nicholasnloehrke/87s_research/boards/controller/pcb/symbols/PJSD03TS-AU_R1_000A1/PJSD03TS-AU_R1_000A1.step

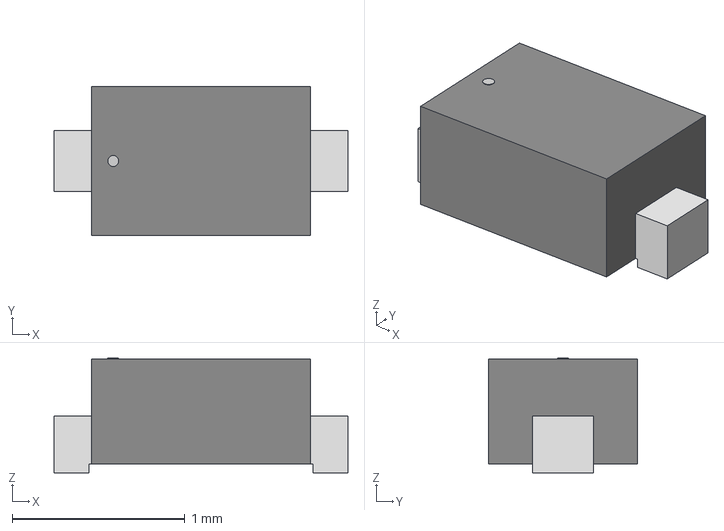
[picture p28: CAD file, 2025-05-06]
boards/controller/pcb/symbols/PJSD03TS-AU_R1_000A1/PJSD03TS-AU_R1_000A1.step
1.70 x 0.864 x 0.663 mm
