nicholasnloehrke/87s_research/boards/controller/pcb/symbols/RH100-16.000-18-2030-EXT-TR/RH100-16.000-18-2030-EXT-TR.step

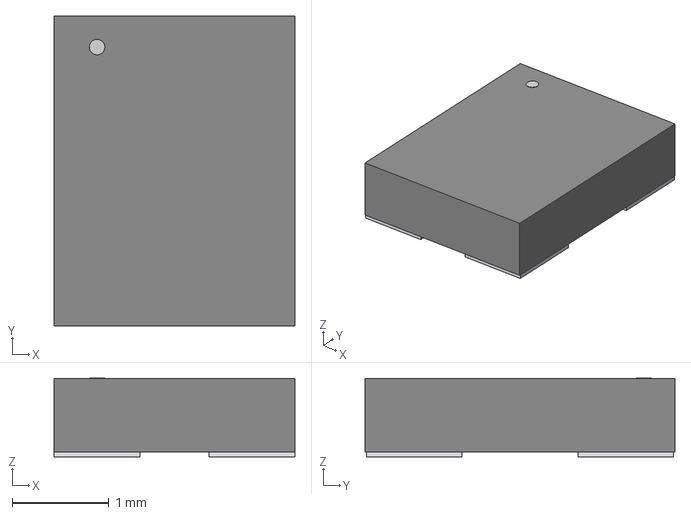
[picture p29: CAD file, 2025-05-06]
boards/controller/pcb/symbols/RH100-16.000-18-2030-EXT-TR/RH100-16.000-18-2030-EXT-TR.step
2.49 x 3.20 x 0.815 mm
