nicholasnloehrke/87s_research/boards/controller/pcb/symbols/SISA35DN-T1-GE3/SISA35DN-T1-GE3.STEP

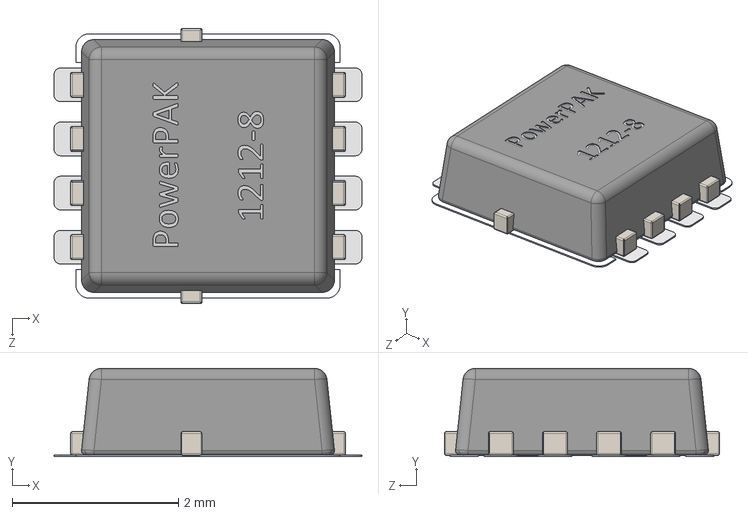
[picture p30: CAD file, 2024-11-11]
boards/controller/pcb/symbols/SISA35DN-T1-GE3/SISA35DN-T1-GE3.STEP
3.70 x 1.06 x 3.30 mm
