nicholasnloehrke/87s_research/boards/controller/pcb/symbols/SSM3J372R_LF/SSM3J372R_LF.step

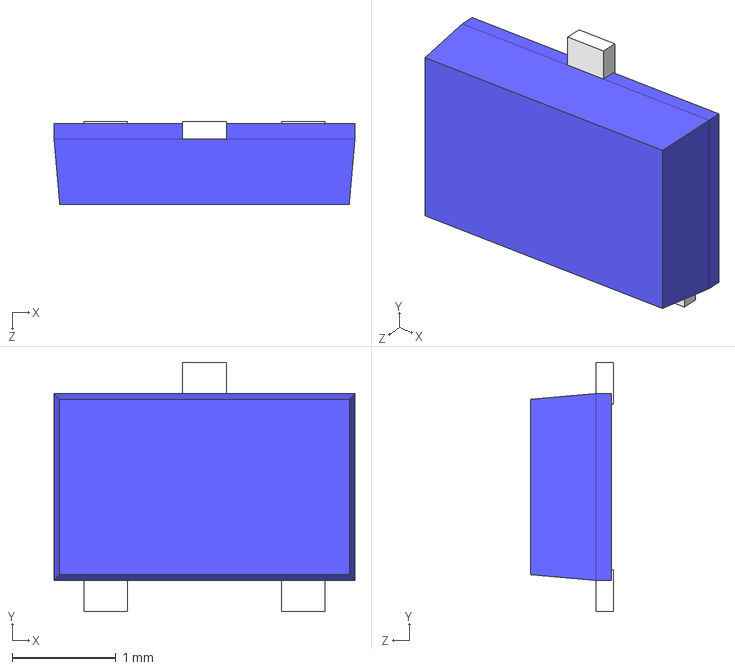
[picture p31: CAD file, 2025-05-06]
boards/controller/pcb/symbols/SSM3J372R_LF/SSM3J372R_LF.step
2.90 x 2.40 x 0.8 mm
