nicholasnloehrke/87s_research/boards/controller/pcb/symbols/XT30/XT30.stp

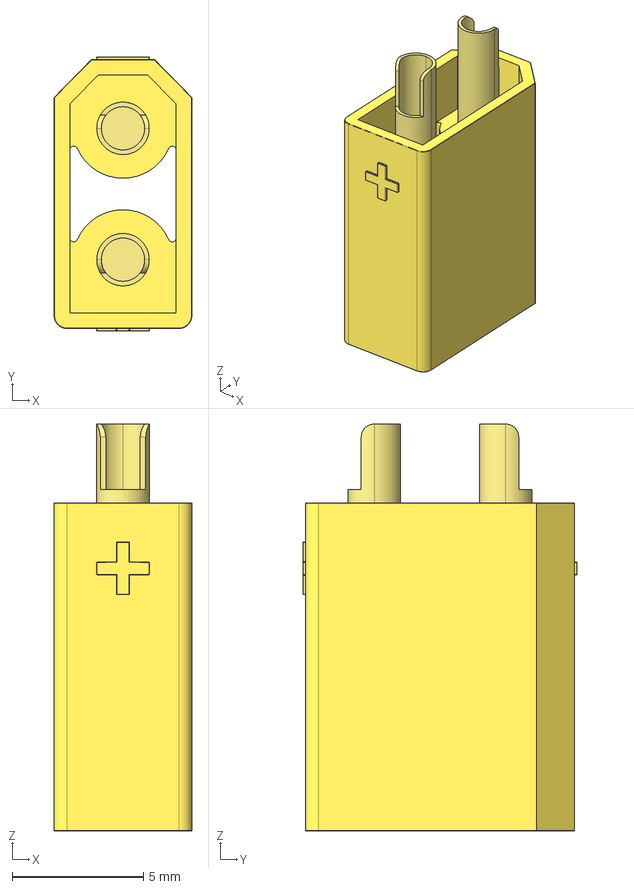
[picture p32: CAD file, 2024-11-11]
boards/controller/pcb/symbols/XT30/XT30.stp
5.25 x 10.4 x 15.5 mm
