nicholasnloehrke/87s_research/boards/controller_mockup/mockup_for_reference_only/mockup/300SPxJ1xxxM2xE.stp

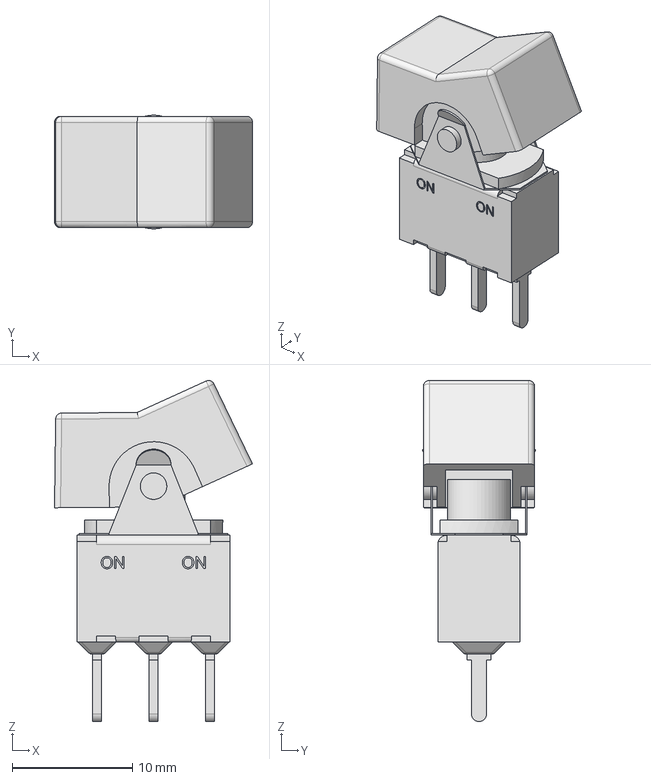
[picture p33: CAD file, 2025-03-07]
boards/controller_mockup/mockup_for_reference_only/mockup/300SPxJ1xxxM2xE.stp
16.5 x 9.45 x 28.4 mm
