nicholasnloehrke/87s_research/boards/controller_mockup/mockup_for_reference_only/mockup/USB4120_03_C/USB4120-03-C.step

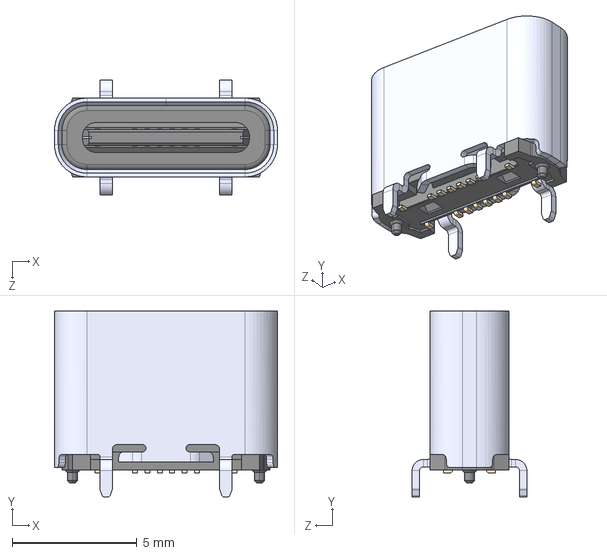
[picture p34: CAD file, 2025-03-07]
boards/controller_mockup/mockup_for_reference_only/mockup/USB4120_03_C/USB4120-03-C.step
8.94 x 7.45 x 4.60 mm
