nicholasnloehrke/87s_research/boards/power_supply/pcb/symbols/1N4148W-13-F/1N4148W-13-F.STEP

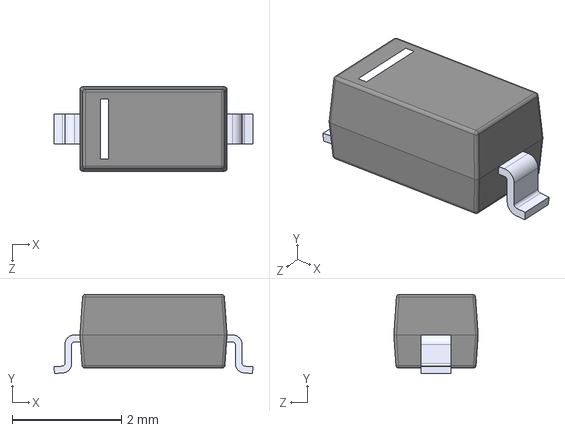
[picture p35: CAD file, 2024-11-08]
boards/power_supply/pcb/symbols/1N4148W-13-F/1N4148W-13-F.STEP
3.65 x 1.45 x 1.55 mm
