nicholasnloehrke/87s_research/boards/power_supply/pcb/symbols/LM5181NGUR/LM5181NGUR.stp

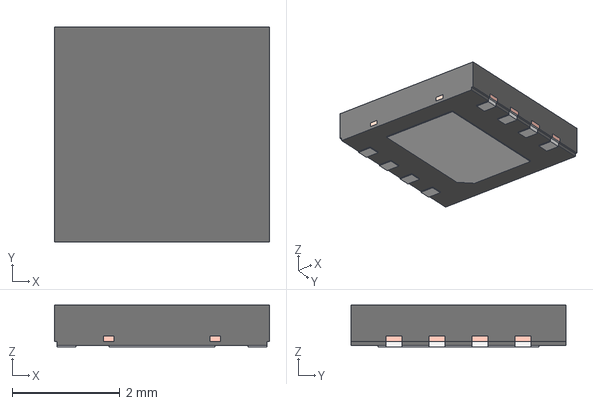
[picture p36: CAD file, 2024-09-19]
boards/power_supply/pcb/symbols/LM5181NGUR/LM5181NGUR.stp
4.00 x 4.00 x 0.775 mm
BODY-SON_AF0
FRAME-NGU0008C_AF0
