nicholasnloehrke/87s_research/boards/power_supply/pcb/symbols/MP2759GQ-0000-Z/MP2759GQ-0000-Z.iges

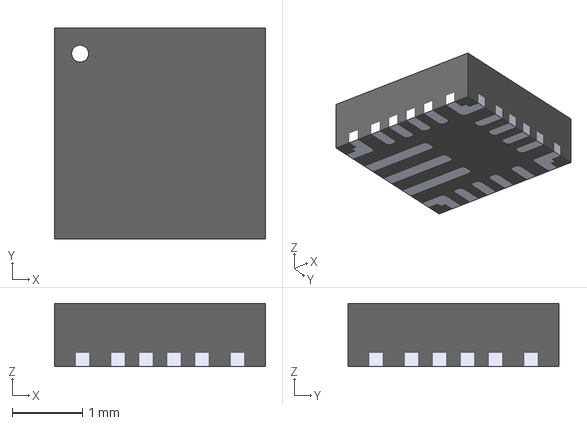
[picture p37: CAD file, 2024-11-11]
boards/power_supply/pcb/symbols/MP2759GQ-0000-Z/MP2759GQ-0000-Z.iges
3.00 x 3.00 x 0.9 mm
