nicholasnloehrke/87s_research/boards/power_supply/pcb/symbols/PTS526_SK15_SMTR2_LFS/PTS526_SK15_SMTR2_LFS.STEP

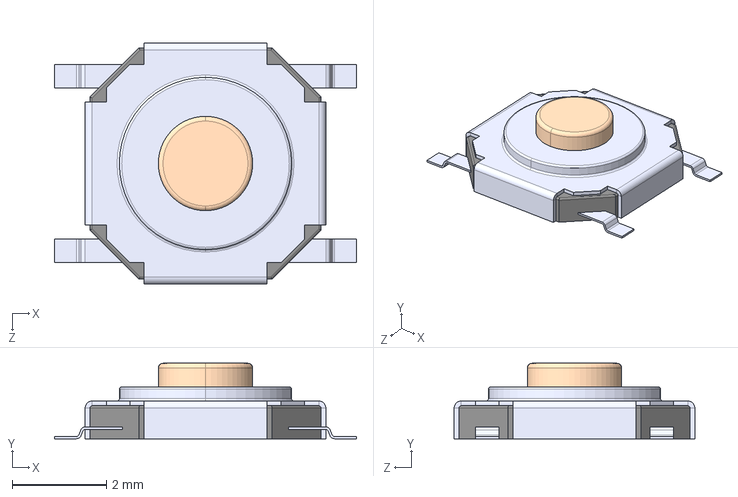
[picture p38: CAD file, 2024-10-13]
boards/power_supply/pcb/symbols/PTS526_SK15_SMTR2_LFS/PTS526_SK15_SMTR2_LFS.STEP
6.40 x 1.60 x 5.10 mm
