nicholasnloehrke/87s_research/boards/power_supply/pcb/symbols/SK34SMA-3G/SK34SMA-3G.step

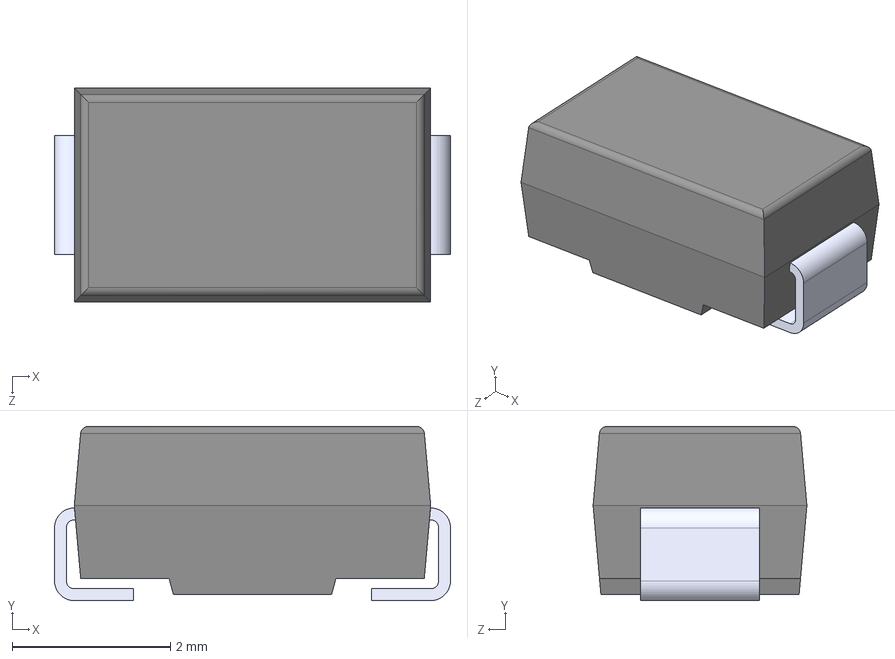
[picture p39: CAD file, 2024-11-08]
boards/power_supply/pcb/symbols/SK34SMA-3G/SK34SMA-3G.step
5.00 x 2.20 x 2.70 mm
