nicholasnloehrke/87s_research/boards/power_supply/pcb/symbols/SMAZ22-13-F/SMAZ22-13-F.step

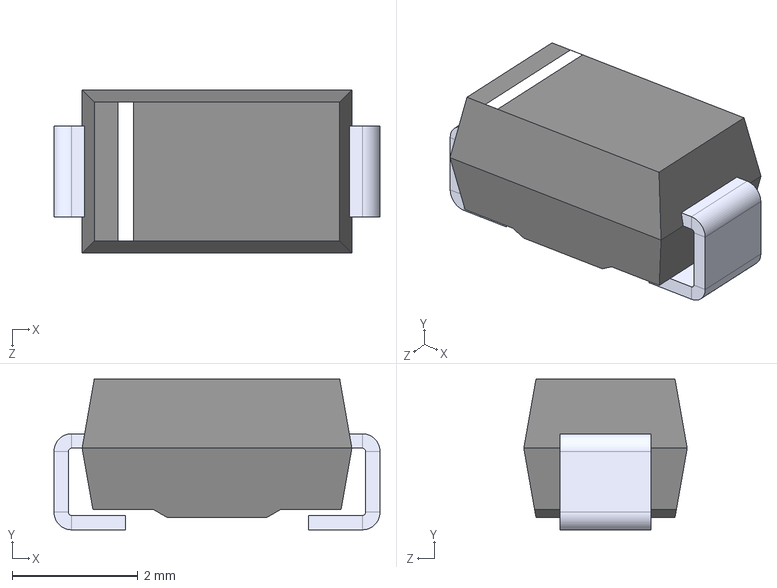
[picture p40: CAD file, 2024-11-11]
boards/power_supply/pcb/symbols/SMAZ22-13-F/SMAZ22-13-F.step
5.20 x 2.40 x 2.60 mm
