nicholasnloehrke/87s_research/boards/power_supply/pcb/symbols/USB4105-GF-A/USB4105-GF-A.step

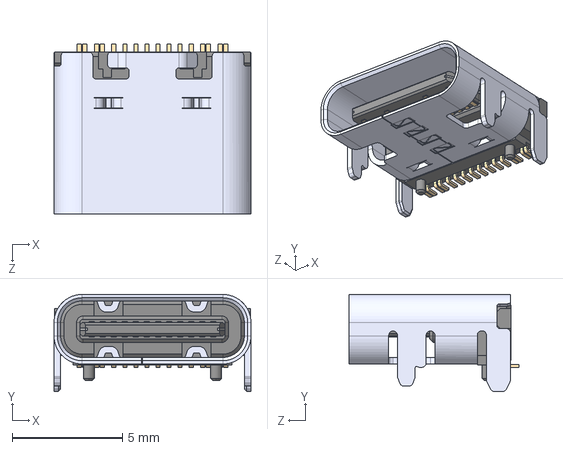
[picture p41: CAD file, 2024-11-11]
boards/power_supply/pcb/symbols/USB4105-GF-A/USB4105-GF-A.step
8.94 x 4.41 x 7.71 mm
