nicholasnloehrke/87s_research/boards/power_supply/pcb/symbols/USBLC6-2SC6/USBLC6-2SC6.step

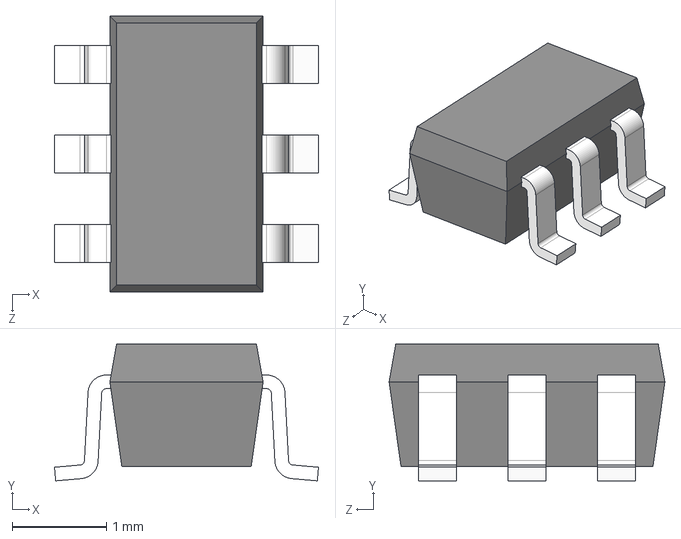
[picture p42: CAD file, 2024-11-08]
boards/power_supply/pcb/symbols/USBLC6-2SC6/USBLC6-2SC6.step
2.80 x 1.45 x 2.92 mm
