nicholasnloehrke/87s_research/kicad/power_supply/symbols/750313445/SOIC_13445_WRE.step

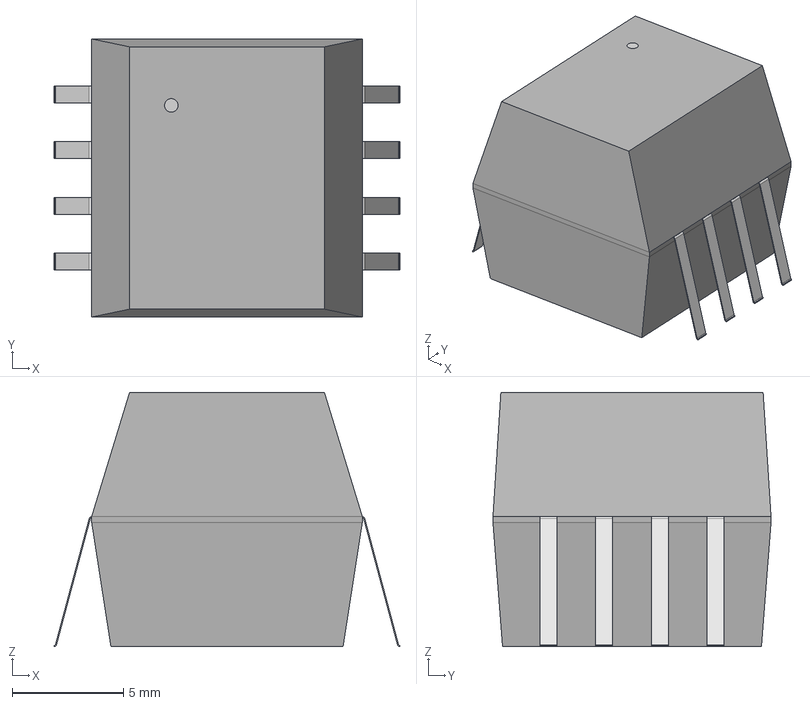
[picture p43: CAD file, 2024-09-19]
kicad/power_supply/symbols/750313445/SOIC_13445_WRE.step
15.5 x 12.5 x 11.4 mm
