nicholasnloehrke/87s_research/kicad/power_supply/symbols/DMN65D8L_7/SOT-23_2P9X1P3_DIO.step

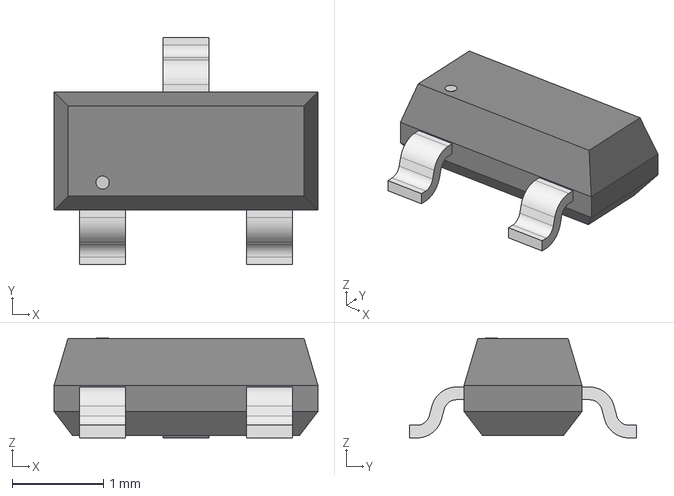
[picture p44: CAD file, 2024-09-16]
kicad/power_supply/symbols/DMN65D8L_7/SOT-23_2P9X1P3_DIO.step
2.90 x 2.49 x 1.09 mm
