nicholasnloehrke/87s_research/kicad/power_supply/symbols/PDZVTR9_1B/DIO_PDZVTFT_ROM.step

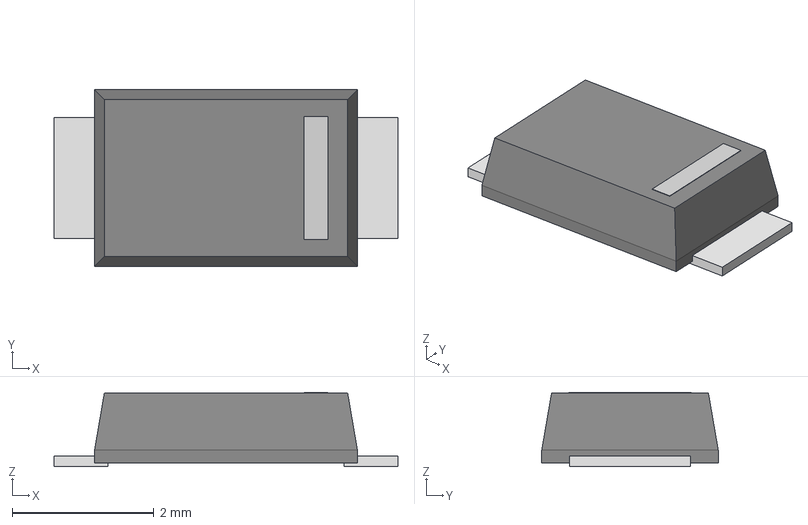
[picture p45: CAD file, 2024-09-19]
kicad/power_supply/symbols/PDZVTR9_1B/DIO_PDZVTFT_ROM.step
4.85 x 2.49 x 1.05 mm
