nicholasnloehrke/87s_research/kicad/power_supply/symbols/RTBS60M/RTBS60M.step

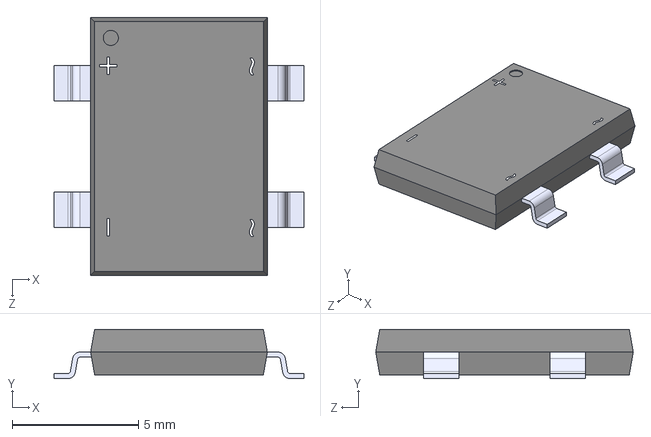
[picture p46: CAD file, 2024-09-16]
kicad/power_supply/symbols/RTBS60M/RTBS60M.step
9.90 x 1.95 x 10.2 mm
