nicholasnloehrke/87s_research/kicad/power_supply/symbols/SISS94DN_T1_GE3/model/SISS94DN-T1-GE3.FCStd

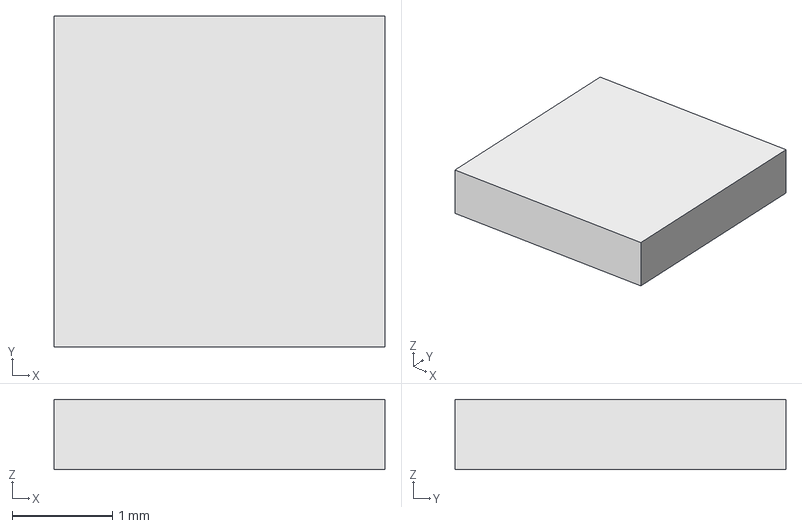
[picture p47: CAD file, 2024-09-24]
kicad/power_supply/symbols/SISS94DN_T1_GE3/model/SISS94DN-T1-GE3.FCStd
3.30 x 3.30 x 0.7 mm
