nicholasnloehrke/87s_research/kicad/power_supply/symbols/TPS562243DRLR/DRL0006A.stp

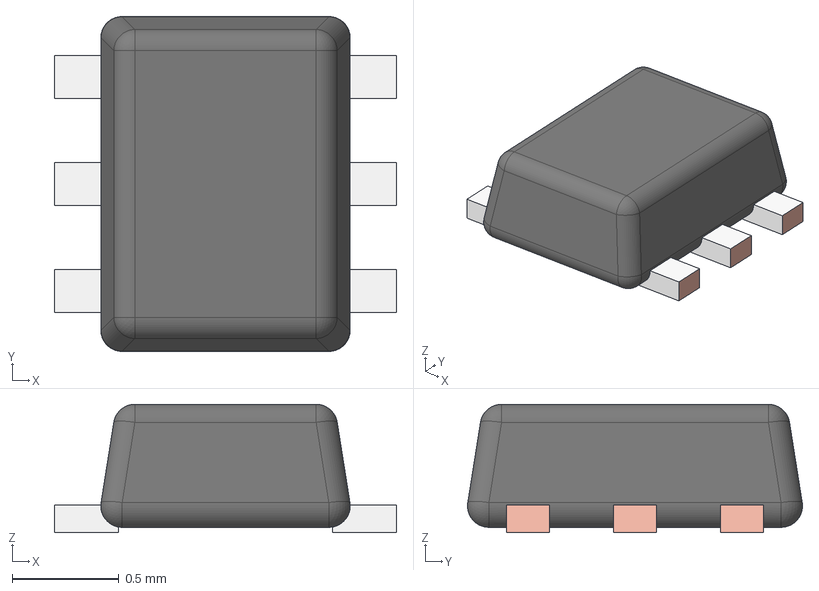
[picture p48: CAD file, 2024-10-03]
kicad/power_supply/symbols/TPS562243DRLR/DRL0006A.stp
1.60 x 1.57 x 0.6 mm
FRAME-DRL0006A
BODY-SOT
PIN1-ID
