nicholasnloehrke/87s_research/mechanical/encoder_pec12r-4x20f-sxxxx.stp

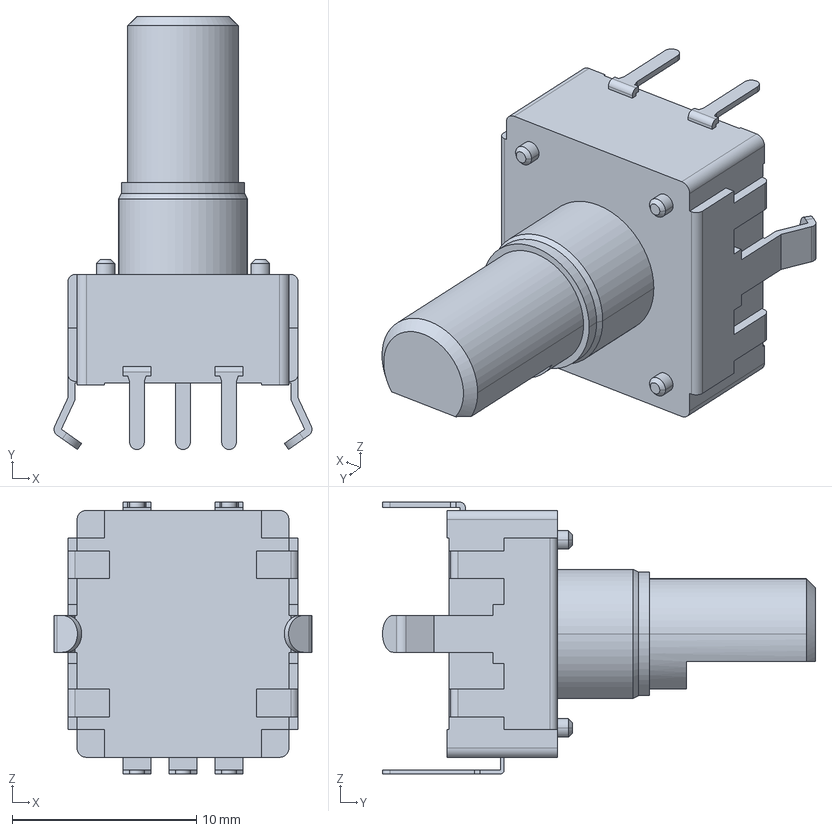
[picture p49: CAD file, 2025-02-06]
mechanical/encoder_pec12r-4x20f-sxxxx.stp
14.0 x 23.5 x 14.7 mm
