nicholasnloehrke/87s_research/boards/controller_mockup/mockup_for_reference_only/mockup/Unnamed2-P__E-Switch Secure_3D_MODELS_STP_FORMAT_300SPxJ1xxxM2xE.stp.step

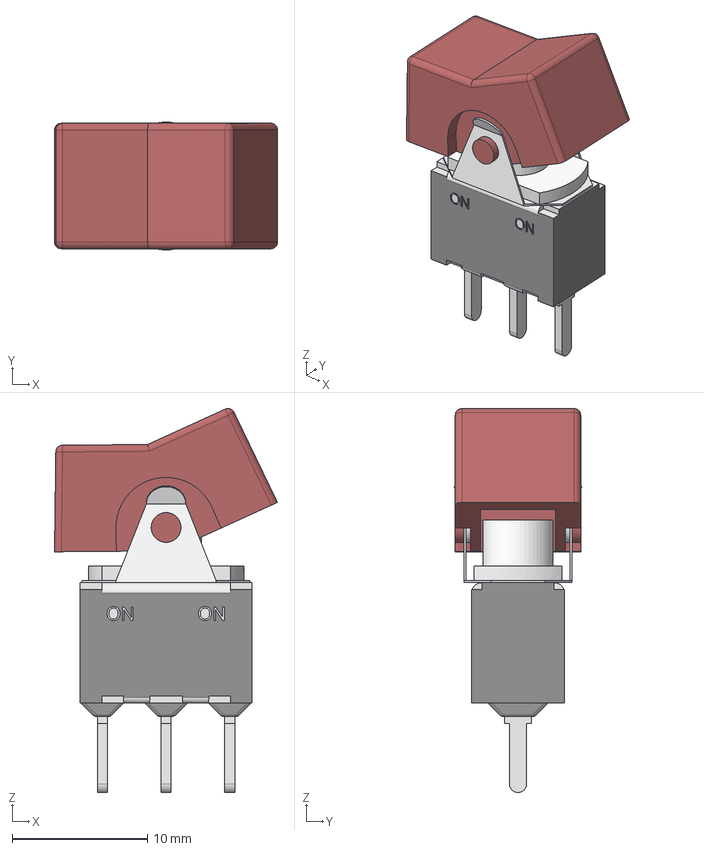
[picture p50: CAD file, 2025-03-07]
boards/controller_mockup/mockup_for_reference_only/mockup/Unnamed2-P__E-Switch Secure_3D_MODELS_STP_FORMAT_300SPxJ1xxxM2xE.stp.step
16.5 x 9.45 x 28.4 mm
