nicholasnloehrke/87s_research/boards/controller_mockup/mockup_for_reference_only/mockup/encoder-with-color.step

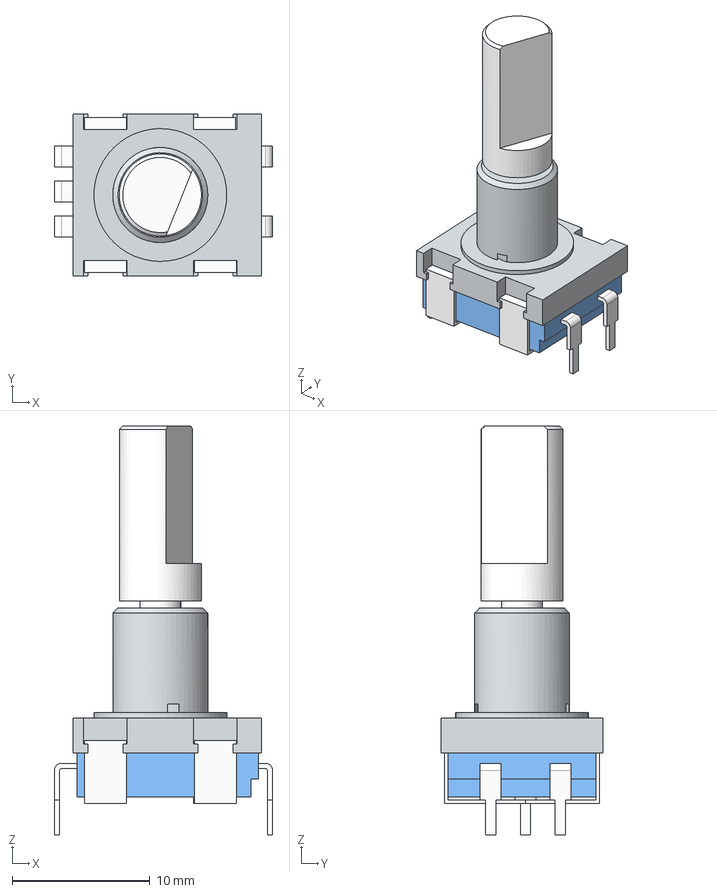
[picture p51: CAD file, 2025-03-07]
boards/controller_mockup/mockup_for_reference_only/mockup/encoder-with-color.step
15.8 x 11.8 x 29.7 mm
mtg flange
pins_encoder body_2 x 5
shaft_encoder
body_encoder
