nicholasnloehrke/87s_research/boards/controller-old/pcb/controller.kicad_pcb

## KiCad design boards/controller-old/pcb/controller.kicad_pcb (2024-11-23, an earlier design)

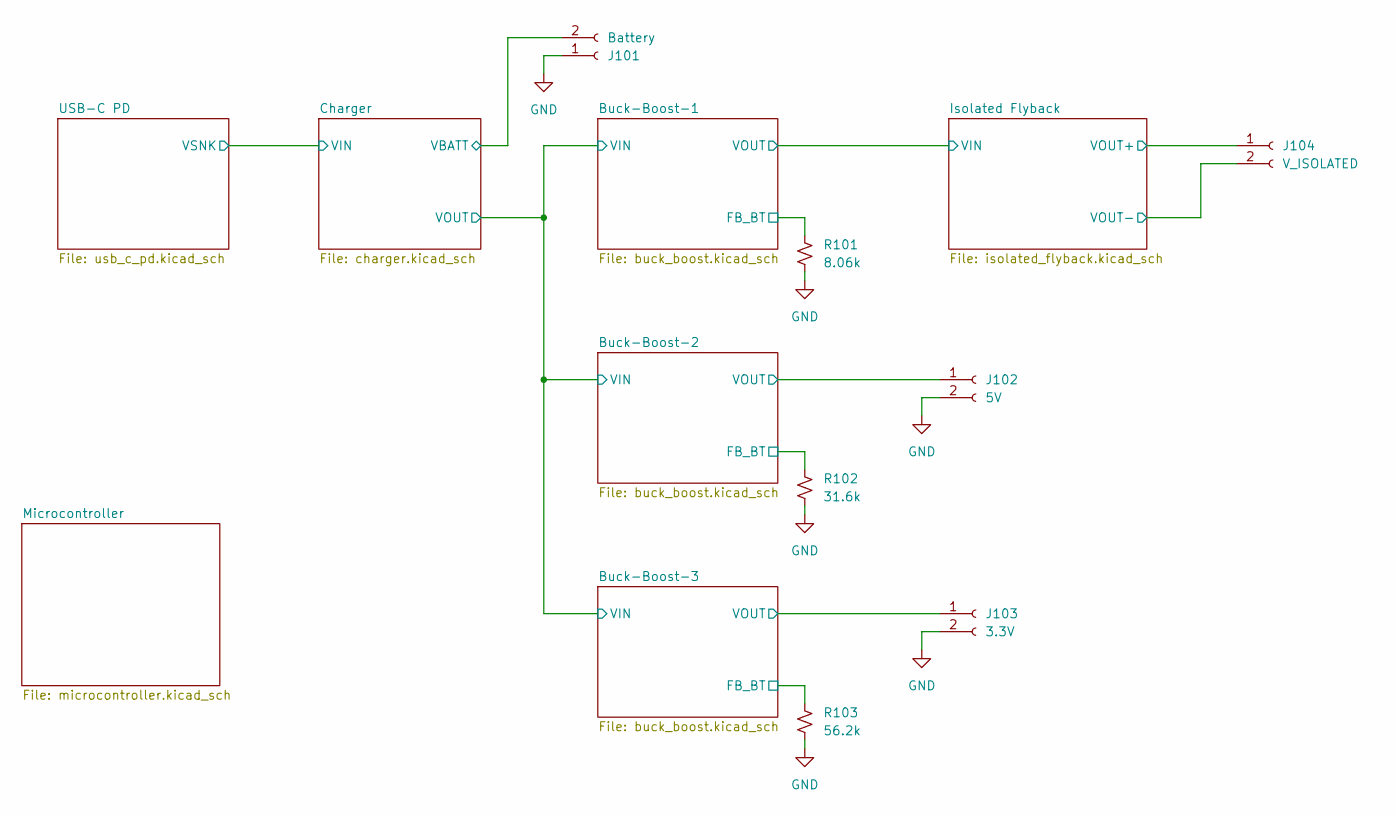
[picture p77: schematic controller.kicad_sch, Power Supply]

Parts:
J101: Battery; AMASS_XT30U-F_1x02_P5.0mm_Vertical
J102: 5V; JST_XH_B2B-XH-A_1x02_P2.50mm_Vertical
J103: 3.3V; JST_XH_B2B-XH-A_1x02_P2.50mm_Vertical
J104: V_ISOLATED; JST_XH_B2B-XH-A_1x02_P2.50mm_Vertical
R101: 8.06k; R_0603_1608Metric
R102: 31.6k; R_0603_1608Metric
R103: 56.2k; R_0603_1608Metric

Connections:
/Buck-Boost-1/FB_BT: R101.2; also elsewhere on the board
/Buck-Boost-2/FB_BT: R102.2; also elsewhere on the board
/Buck-Boost-2/VOUT: J102.1; also elsewhere on the board
/Buck-Boost-3/FB_BT: R103.2; also elsewhere on the board
/Buck-Boost-3/VOUT: J103.1; also elsewhere on the board
/Charger/VBATT: J101.2; also elsewhere on the board
/Isolated Flyback/VOUT+: J104.1; also elsewhere on the board
/Isolated Flyback/VOUT-: J104.2; also elsewhere on the board
GND: J101.1, J102.2, J103.2, R101.1, R102.1, R103.1; also elsewhere on the board

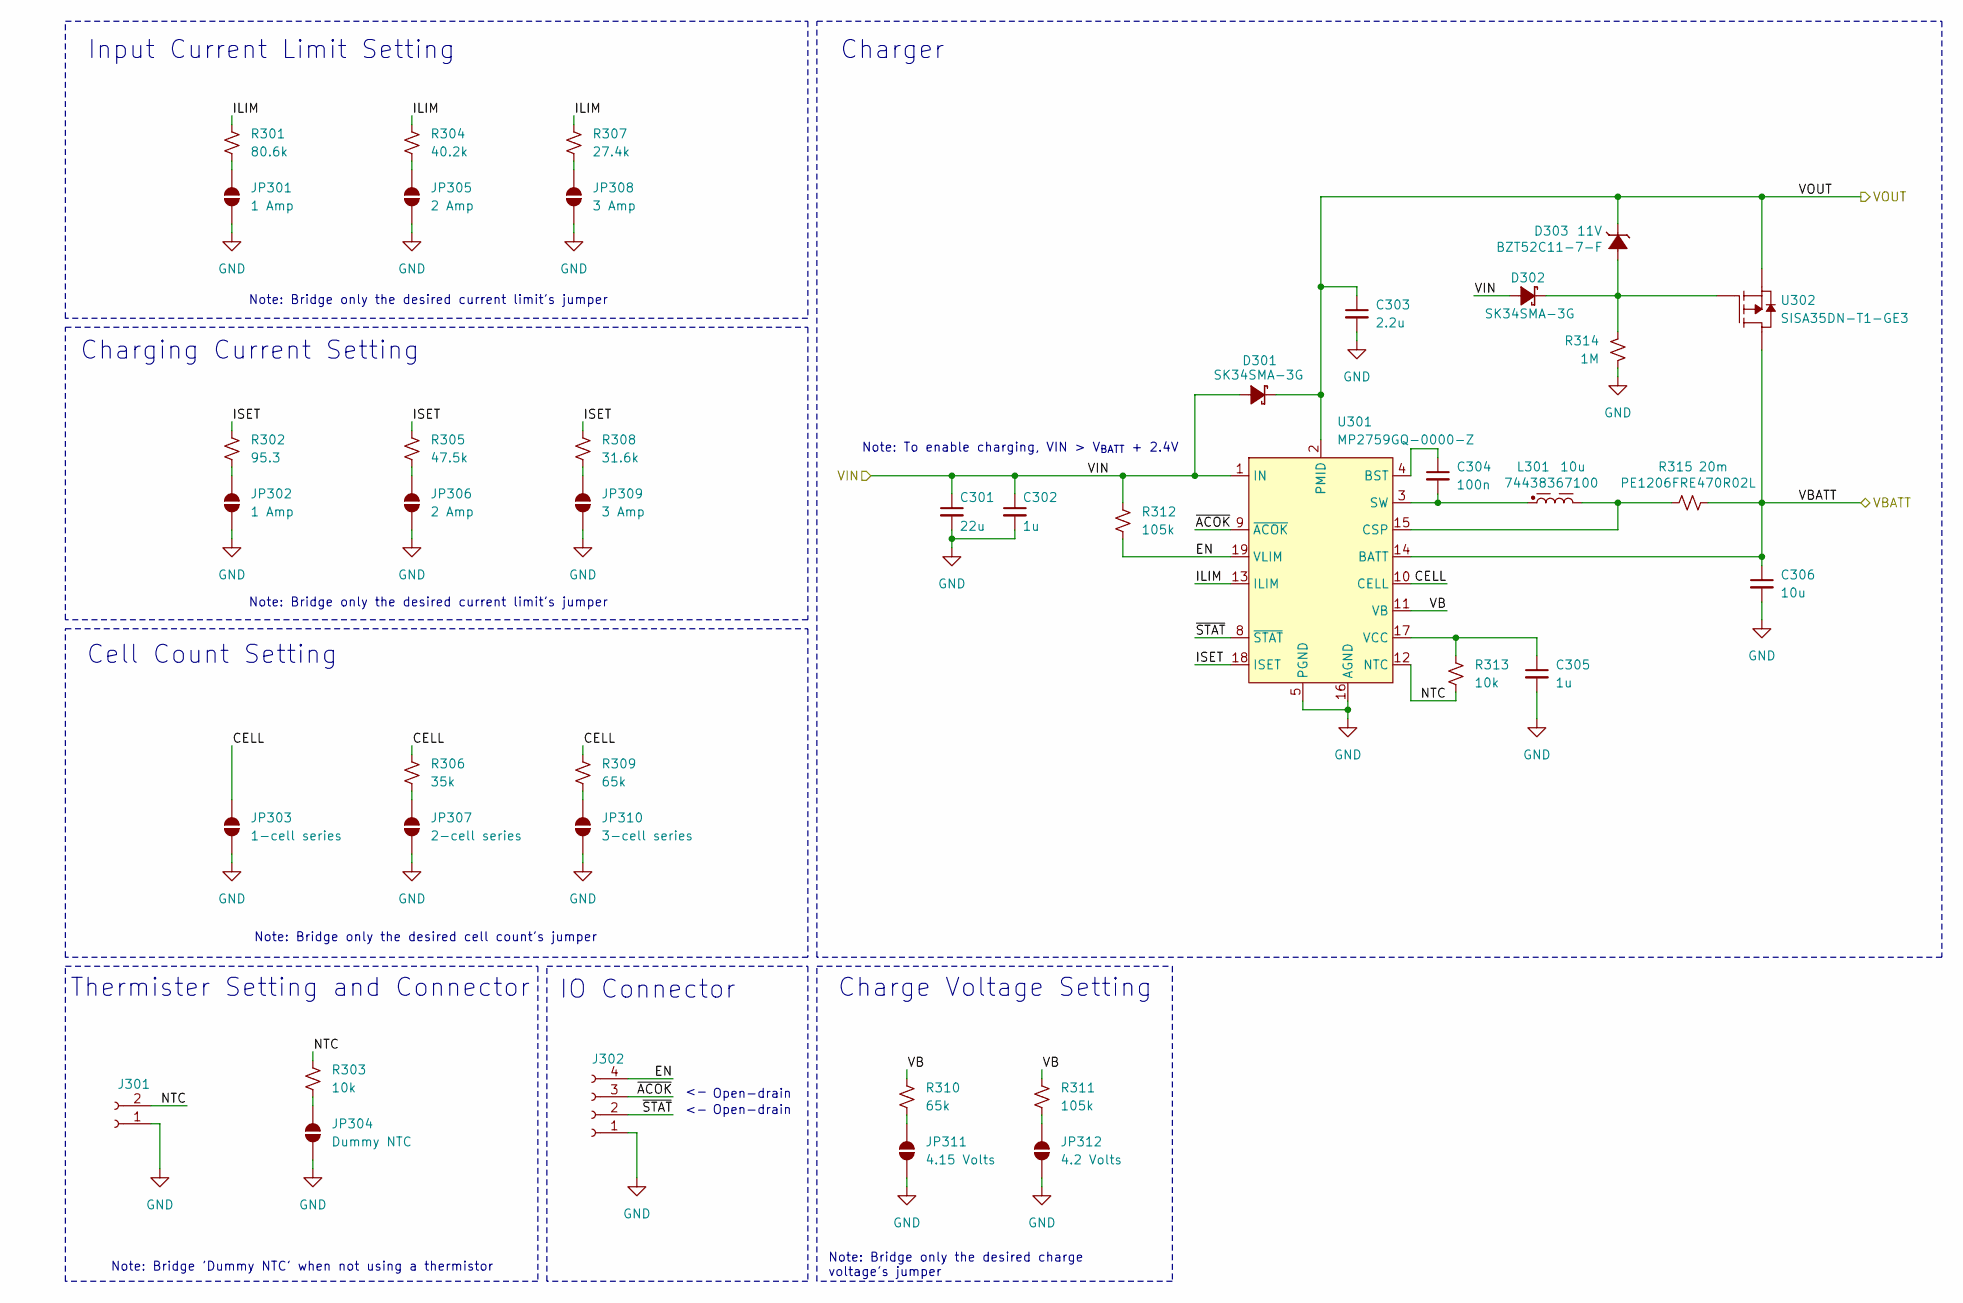
[picture p78: schematic charger.kicad_sch]

Parts:
C301: 22u; C_1206_3216Metric
C302, C305: 1u; C_0603_1608Metric
C303: 2.2u; C_1206_3216Metric
C304: 100n; C_0603_1608Metric
C306: 10u; C_0805_2012Metric
D301, D302: SK34SMA-3G; MPN SK34SMA-3G
D303: 11V; BZT52C11-7-F; MPN BZT52C11-7-F
J301: Conn_01x02_Socket; JST_XH_B2B-XH-A_1x02_P2.50mm_Vertical
J302: Conn_01x04_Socket; JST_XH_B4B-XH-A_1x04_P2.50mm_Vertical
JP301, JP302: 1 Amp; SolderJumper-2_P1.3mm_Open_RoundedPad1.0x1.5mm
JP303: 1-cell series; SolderJumper-2_P1.3mm_Open_RoundedPad1.0x1.5mm
JP304: Dummy NTC; SolderJumper-2_P1.3mm_Open_RoundedPad1.0x1.5mm
JP305, JP306: 2 Amp; SolderJumper-2_P1.3mm_Open_RoundedPad1.0x1.5mm
JP307: 2-cell series; SolderJumper-2_P1.3mm_Open_RoundedPad1.0x1.5mm
JP308, JP309: 3 Amp; SolderJumper-2_P1.3mm_Open_RoundedPad1.0x1.5mm
JP310: 3-cell series; SolderJumper-2_P1.3mm_Open_RoundedPad1.0x1.5mm
JP311: 4.15 Volts; SolderJumper-2_P1.3mm_Open_RoundedPad1.0x1.5mm
JP312: 4.2 Volts; SolderJumper-2_P1.3mm_Open_RoundedPad1.0x1.5mm
L301: 10u; 74438367100; MPN 74438367100
R301: 80.6k; R_0603_1608Metric
R302: 95.3; R_0603_1608Metric
R303, R313: 10k; R_0603_1608Metric
R304: 40.2k; R_0603_1608Metric
R305: 47.5k; R_0603_1608Metric
R306: 35k; R_0603_1608Metric
R307: 27.4k; R_0603_1608Metric
R308: 31.6k; R_0603_1608Metric
R309, R310: 65k; R_0603_1608Metric
R311, R312: 105k; R_0603_1608Metric
R314: 1M; R_0603_1608Metric
R315: 20m; PE1206FRE470R02L; MPN PE1206FRE470R02L
U301: MP2759GQ-0000-Z; MPN MP2759GQ-0000-Z
U302: SISA35DN-T1-GE3; MPN SISA35DN-T1-GE3

Connections:
/Buck-Boost-1/VIN: C303.1, D301.1, D303.1, U301.2 (PMID), U302.1; also elsewhere on the board
/Charger/CELL: JP303.2 (B), R306.1, R309.1, U301.10 (CELL)
/Charger/EN: J302.4, R312.2, U301.19 (VLIM)
/Charger/ILIM: R301.1, R304.1, R307.1, U301.13 (ILIM)
/Charger/ISET: R302.1, R305.1, R308.1, U301.18 (ISET)
/Charger/NTC: J301.2, R303.1, R313.2, U301.12 (NTC)
/Charger/VB: R310.1, R311.1, U301.11 (VB)
/Charger/VBATT: C306.1, R315.2, U301.14 (BATT), U302.5; also elsewhere on the board
/Charger/VIN: C301.1, C302.1, D301.2, D302.2, R312.1, U301.1 (IN); also elsewhere on the board
/Charger/~ACOK: J302.3, U301.9 (~ACOK)
/Charger/~STAT: J302.2, U301.8 (~STAT)
GND: C301.2, C302.2, C303.2, C305.2, C306.2, J301.1, J302.1, JP301.1 (A), JP302.1 (A), JP303.1 (A), JP304.1 (A), JP305.1 (A), JP306.1 (A), JP307.1 (A), JP308.1 (A), JP309.1 (A), JP310.1 (A), JP311.1 (A), JP312.1 (A), R314.2, U301.5 (PGND), U301.6 (PGND), U301.7 (PGND), U301.16 (AGND); also elsewhere on the board
unnamed: D302.1, D303.2, R314.1, U302.4
unnamed: JP301.2 (B), R301.2
unnamed: JP302.2 (B), R302.2
unnamed: JP304.2 (B), R303.2
unnamed: JP305.2 (B), R304.2
unnamed: JP306.2 (B), R305.2
unnamed: JP307.2 (B), R306.2
unnamed: JP308.2 (B), R307.2
unnamed: JP309.2 (B), R308.2
unnamed: JP310.2 (B), R309.2
unnamed: JP311.2 (B), R310.2
unnamed: JP312.2 (B), R311.2
unnamed: C304.1, U301.4 (BST)
unnamed: L301.2, R315.1, U301.15 (CSP)
unnamed: C304.2, L301.1, U301.3 (SW)
unnamed: C305.1, R313.1, U301.17 (VCC)

Notes on the sheet:
Note: Bridge only the desired cell count's jumper
Charging Current Setting
Note: Bridge 'Dummy NTC' when not using a thermistor
Thermister Setting and Connector
Cell Count Setting
Charger
Note: Bridge only the desired charge voltage's jumper
IO Connector
Input Current Limit Setting
Note: Bridge only the desired current limit's jumper
Open-drain
Note: To enable charging, VIN > V_{BATT} + 2.4V
Charge Voltage Setting

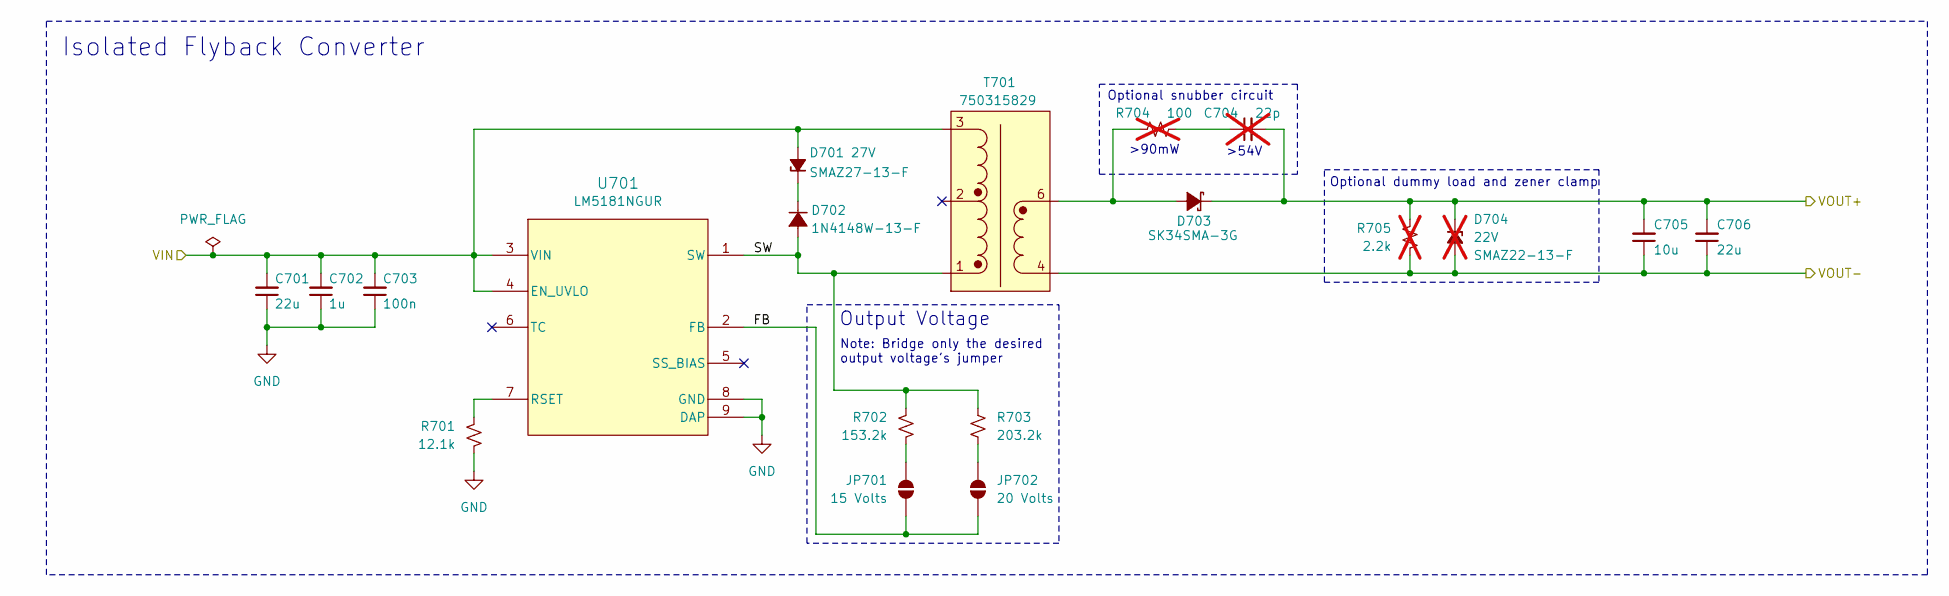
[picture p79: schematic isolated_flyback.kicad_sch, Power Supply]

Parts:
C701, C706: 22u; C_1206_3216Metric
C702: 1u; C_0603_1608Metric
C703: 100n; C_0603_1608Metric
C704: 22p; C_0603_1608Metric; not fitted
C705: 10u; C_0805_2012Metric
D701: 27V; SMAZ27-13-F; MPN SMAZ27-13-F
D702: 1N4148W-13-F; MPN 1N4148W-13-F
D703: SK34SMA-3G; MPN SK34SMA-3G
D704: 22V; SMAZ22-13-F; MPN SMAZ22-13-F; not fitted
JP701: 15 Volts; SolderJumper-2_P1.3mm_Open_RoundedPad1.0x1.5mm
JP702: 20 Volts; SolderJumper-2_P1.3mm_Open_RoundedPad1.0x1.5mm
R701: 12.1k; R_0603_1608Metric
R702: 153.2k; R_0603_1608Metric
R703: 203.2k; R_0603_1608Metric
R704: 100; R_0603_1608Metric; not fitted
R705: 2.2k; R_0603_1608Metric; not fitted
T701: 150u; 750315829; MPN 750315829
U701: NGU0008C-IPC_A; MPN LM5181NGUR

Connections:
/Buck-Boost-1/VOUT: C701.2, C702.2, C703.2, D701.2 (A), T701.3, U701.3 (VIN), U701.4 (EN_UVLO); also elsewhere on the board
/Isolated Flyback/FB: JP701.1 (A), JP702.1 (A), U701.2 (FB)
/Isolated Flyback/SW: D702.2, R702.1, R703.1, T701.1, U701.1 (SW)
/Isolated Flyback/VOUT+: C704.2, C705.2, C706.2, D703.1, D704.1 (K), R705.2; also elsewhere on the board
/Isolated Flyback/VOUT-: C705.1, C706.1, D704.2 (A), R705.1, T701.4; also elsewhere on the board
GND: C701.1, C702.1, C703.1, R701.2, U701.8 (GND), U701.9 (DAP); also elsewhere on the board
unnamed: C704.1, R704.2
unnamed: D701.1 (K), D702.1
unnamed: D703.2, R704.1, T701.6
unnamed: JP701.2 (B), R702.2
unnamed: JP702.2 (B), R703.2
unnamed: R701.1, U701.7 (RSET)

Notes on the sheet:
>90mW
>54V
Optional dummy load and zener clamp
Note: Bridge only the desired output voltage's jumper
Optional snubber circuit
Output Voltage
Isolated Flyback Converter

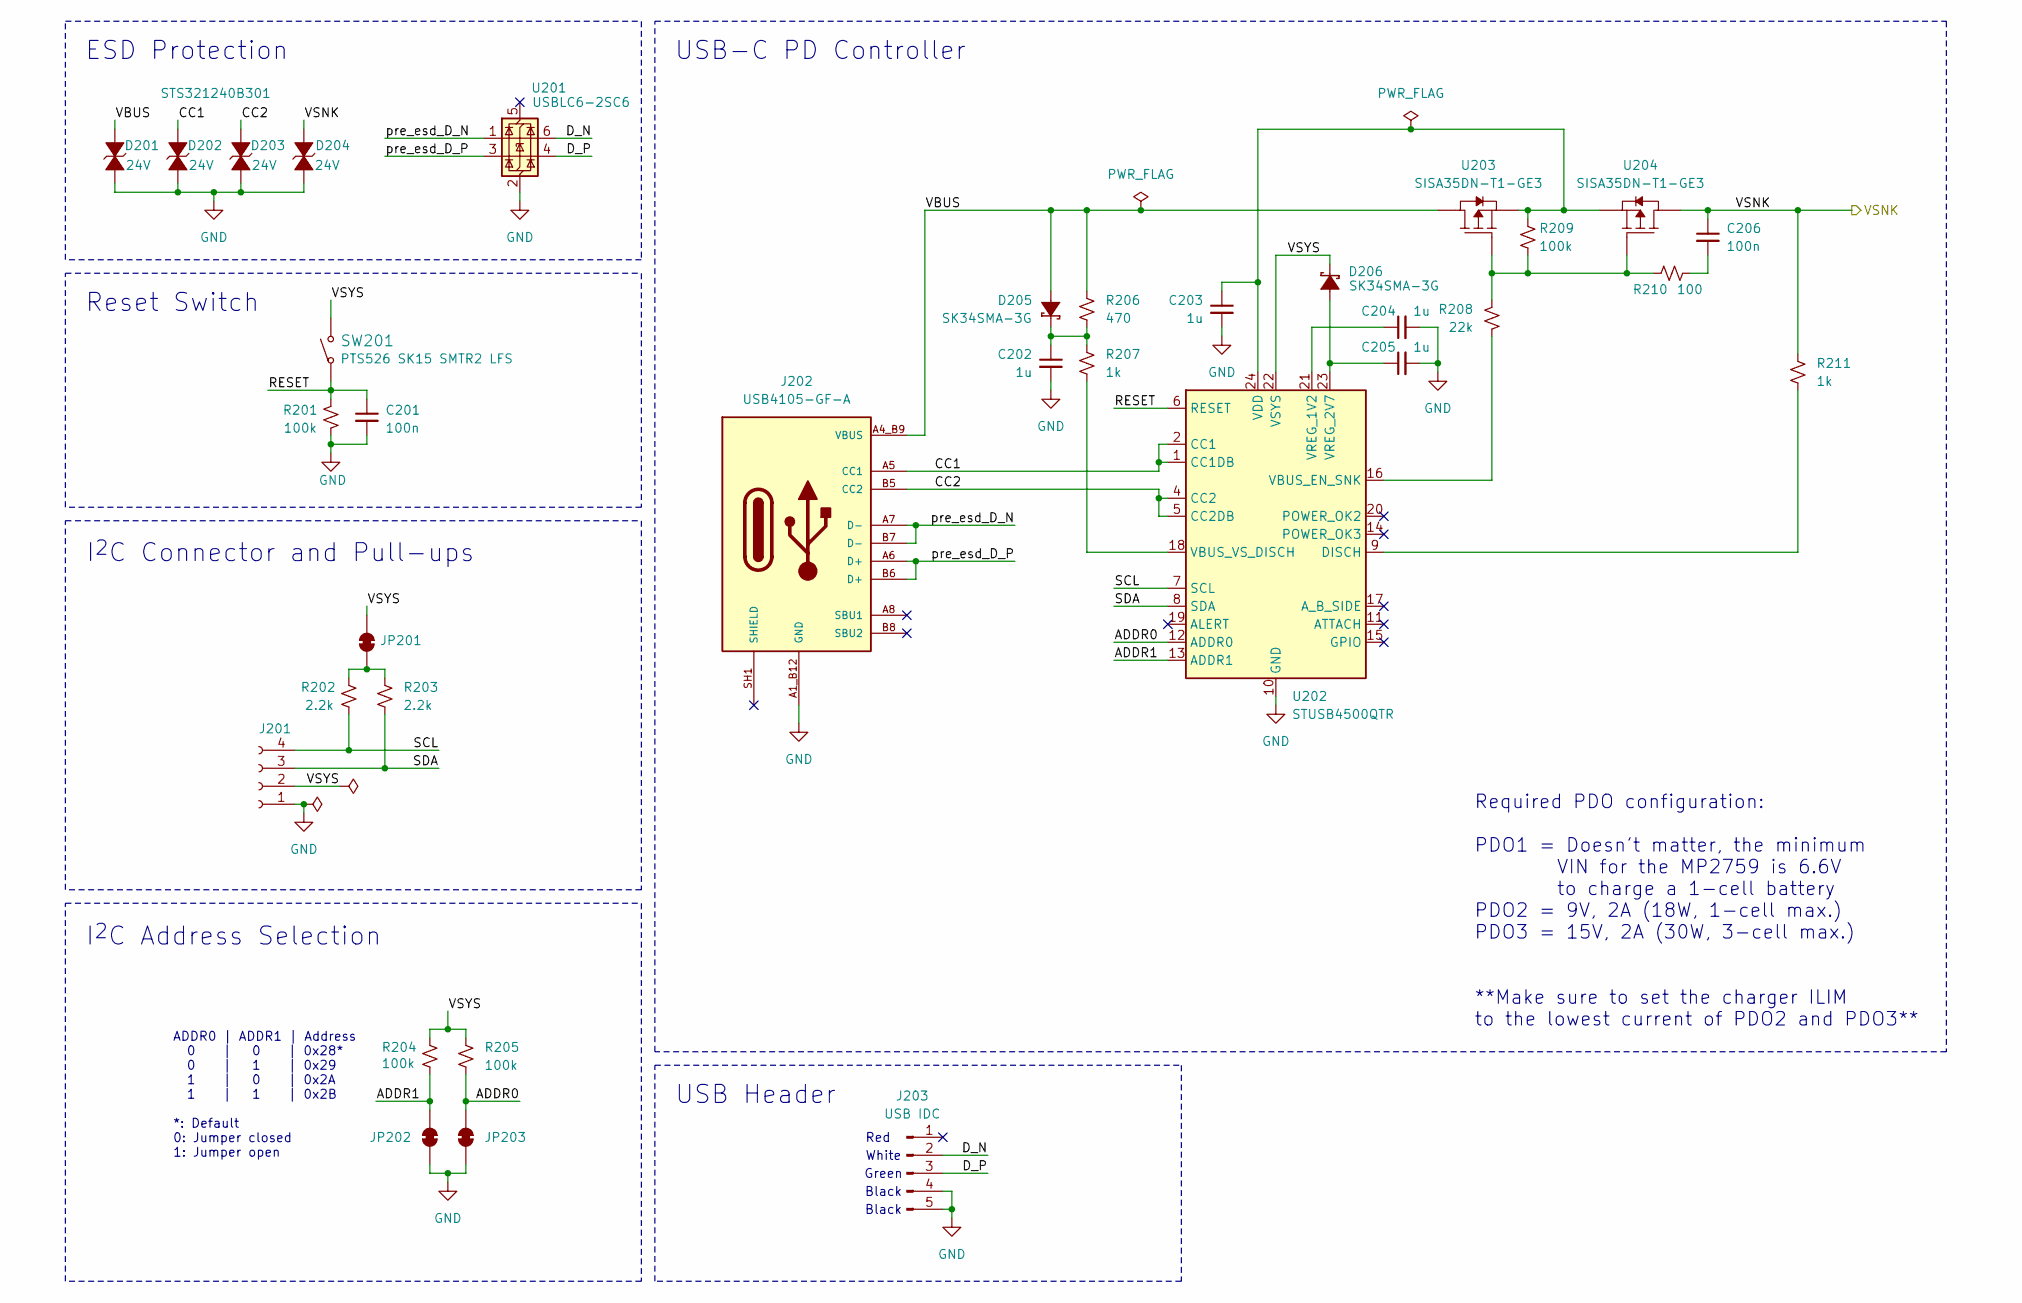
[picture p80: schematic usb_c_pd.kicad_sch]

Parts:
C201, C206: 100n; C_0603_1608Metric
C202, C203, C204, C205: 1u; C_0603_1608Metric
D201, D202, D203, D204: 24V; STS321240B301; MPN STS321240B301
D205, D206: SK34SMA-3G; MPN SK34SMA-3G
J201: Conn_01x04_Socket; PinHeader_1x04_P2.54mm_Vertical
J202: USB4105-GF-A; MPN USB4105-GF-A
J203: USB IDC; PinHeader_1x05_P2.54mm_Vertical
JP201, JP202, JP203: SolderJumper_2_Bridged; SolderJumper-2_P1.3mm_Bridged_RoundedPad1.0x1.5mm
R201, R204, R205, R209: 100k; R_0603_1608Metric
R202, R203: 2.2k; R_0603_1608Metric
R206: 470; R_0603_1608Metric
R207, R211: 1k; R_0603_1608Metric
R208: 22k; R_0603_1608Metric
R210: 100; R_0603_1608Metric
SW201: PTS526 SK15 SMTR2 LFS; SMT_FS; MPN PTS526 SK15 SMTR2 LFS
U201: USBLC6-2P6; SOT-23-6; MPN USBLC6-2SC6
U202: QFN-24-1EP_4x4mm_P0.5mm_EP2.7x2.7mm; MPN STUSB4500QTR
U203, U204: SISA35DN-T1-GE3; MPN SISA35DN-T1-GE3

Connections:
/Charger/VIN: C206.1, D204.2, R211.1, U204.5; also elsewhere on the board
/USB-C PD/ADDR0: JP203.2 (B), R205.2, U202.12 (ADDR0)
/USB-C PD/ADDR1: JP202.1 (A), R204.1, U202.13 (ADDR1)
/USB-C PD/CC1: D202.2, J202.A5 (CC1), U202.1 (CC1DB), U202.2 (CC1)
/USB-C PD/CC2: D203.2, J202.B5 (CC2), U202.4 (CC2), U202.5 (CC2DB)
/USB-C PD/D_N: J203.2, U201.6 (I/O1)
/USB-C PD/D_P: J203.3, U201.4 (I/O2)
/USB-C PD/RESET: C201.1, R201.2, SW201.1, SW201.2, U202.6 (RESET)
/USB-C PD/SCL: J201.4, R202.2, U202.7 (SCL)
/USB-C PD/SDA: J201.3, R203.2, U202.8 (SDA)
/USB-C PD/VSYS: D206.1, J201.2, JP201.2 (B), R204.2, R205.1, SW201.3, SW201.4, U202.22 (VSYS)
/USB-C PD/pre_esd_D_N: J202.A7 (D-), J202.B7 (D-), U201.1 (I/O1)
/USB-C PD/pre_esd_D_P: J202.A6 (D+), J202.B6 (D+), U201.3 (I/O2)
GND: C201.2, C202.2, C203.2, C204.2, C205.2, D201.1, D202.1, D203.1, D204.1, J201.1, J202.A1_B12 (GND), J202.B1_A12 (GND), J203.4, J203.5, JP202.2 (B), JP203.1 (A), R201.1, U201.2 (GND), U202.10 (GND), U202.25 (GND); also elsewhere on the board
unnamed: C202.1, D205.1, R206.2, R207.1
unnamed: C206.2, R210.2
unnamed: JP201.1 (A), R202.1, R203.1
unnamed: R208.1, R209.2, R210.1, U203.4, U204.4
unnamed: R211.2, U202.9 (DISCH)
unnamed: R208.2, U202.16 (VBUS_EN_SNK)
unnamed: R207.2, U202.18 (VBUS_VS_DISCH)
unnamed: C203.1, R209.1, U202.24 (VDD), U203.1, U204.1
unnamed: C204.1, U202.21 (VREG_1V2)
unnamed: C205.1, D206.2, U202.23 (VREG_2V7)
VBUS: D201.2, D205.2, J202.A4_B9 (VBUS), J202.B4_A9 (VBUS), R206.1, U203.5

Notes on the sheet:
I^{2}C Connector and Pull-ups
Black
Green
Reset Switch
Red
USB Header
ESD Protection
USB-C PD Controller
I^{2}C Address Selection
Required PDO configuration: PDO1 = Doesn't matter, the minimum VIN for the MP2759 is 6.6V to charge a 1-cell battery PDO2 = 9V, 2A (18W, 1-cell max.) PDO3 = 15V, 2A (30W, 3-cell max.) **Make sure to set the charger ILIM to the lowest current of PDO2 and PDO3**
White
ADDR0 | ADDR1 | Address 0 | 0 | 0x28* 0 | 1 | 0x29 1 | 0 | 0x2A 1 | 1 | 0x2B *: Default 0: Jumper closed 1: Jumper open

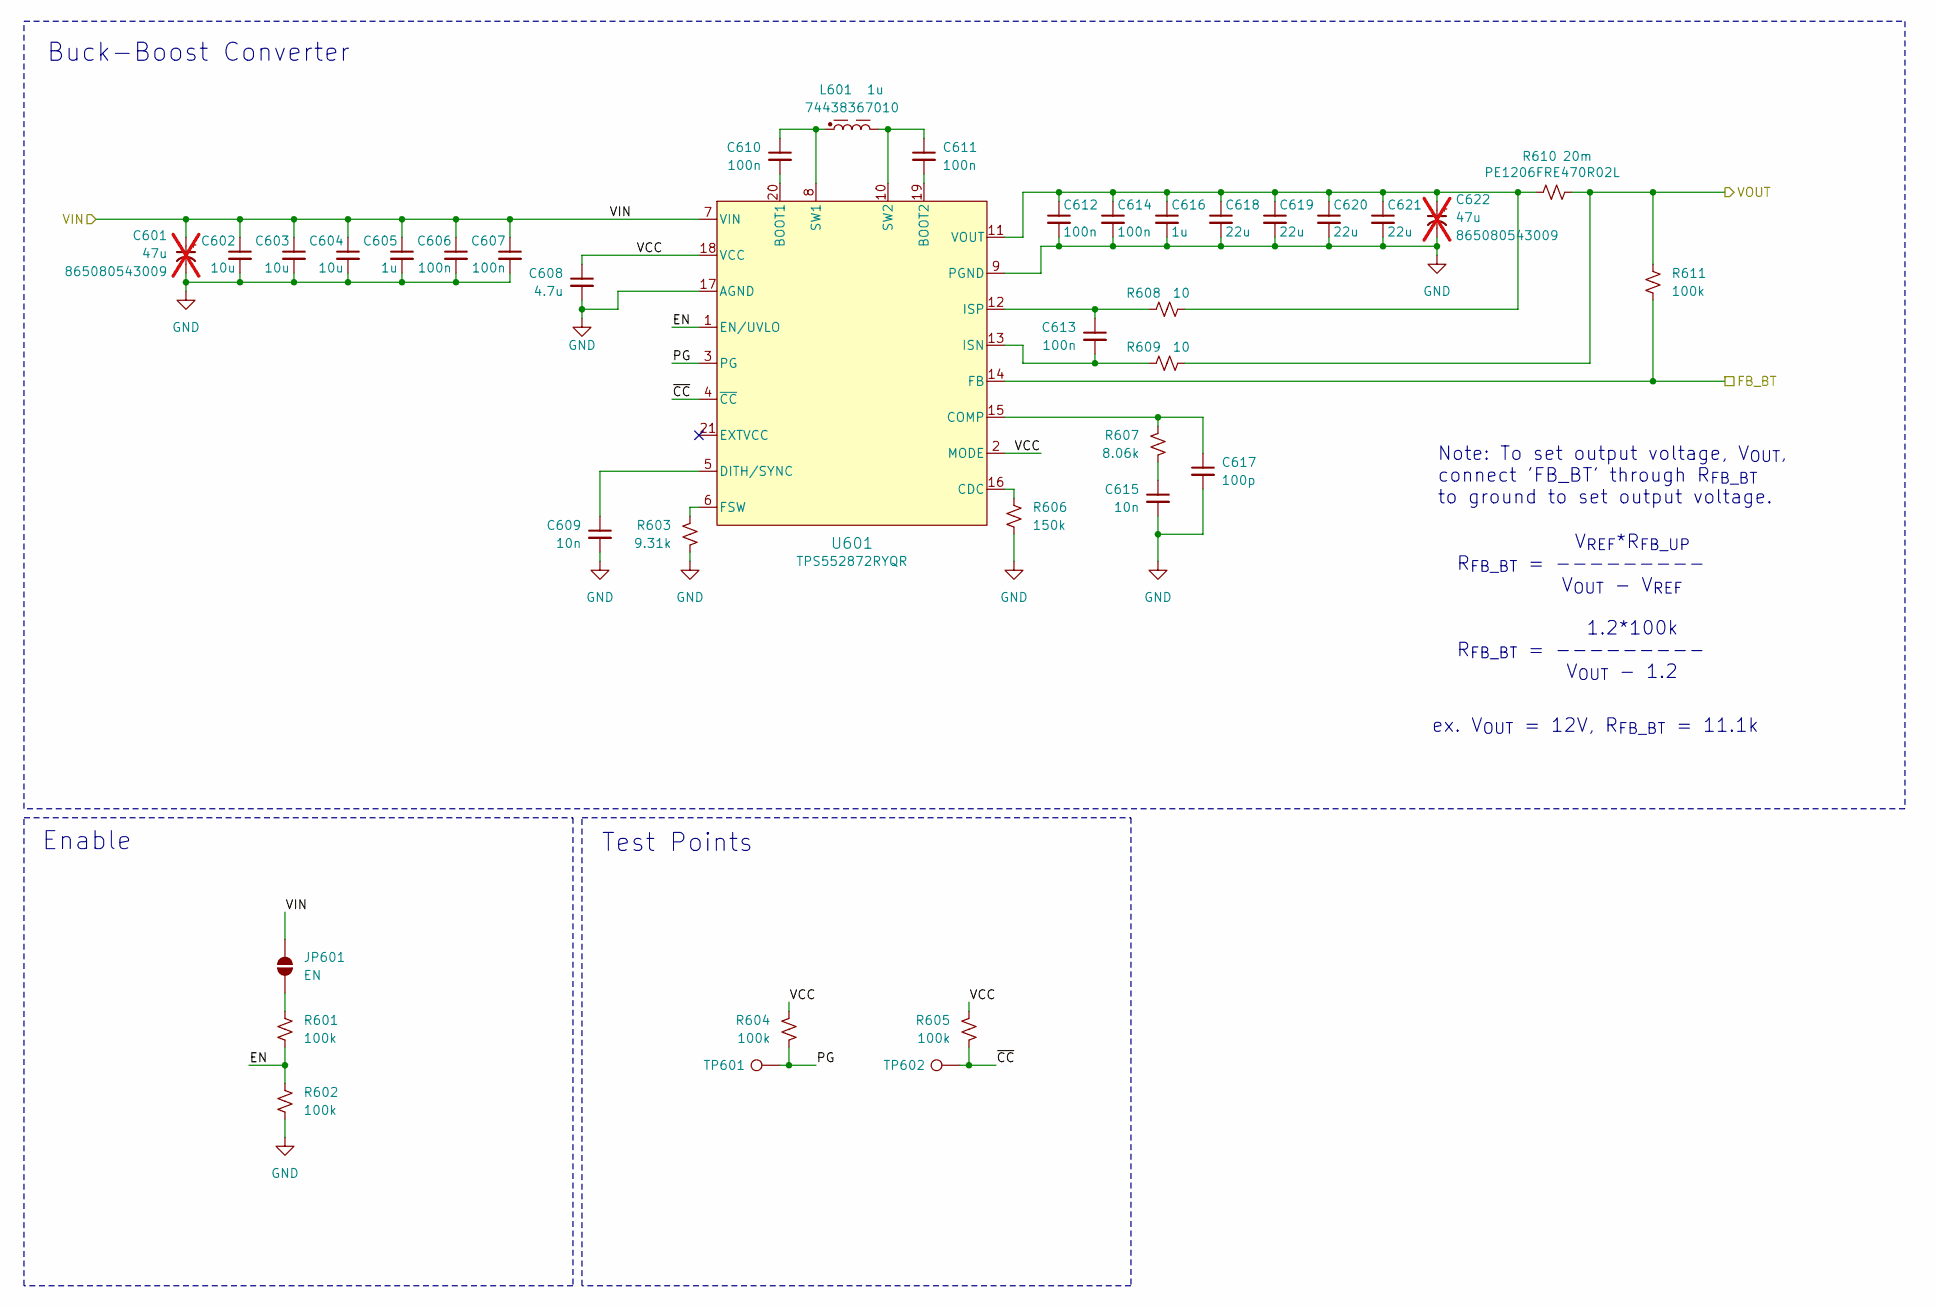
[picture p81: schematic buck_boost.kicad_sch]

Parts:
C601, C622: 47u; 865080543009; MPN 865080543009; not fitted
C602, C603, C604: 10u; C_0805_2012Metric
C605, C616: 1u; C_0603_1608Metric
C606, C607, C610, C611, C612, C613, C614: 100n; C_0603_1608Metric
C608: 4.7u; C_0805_2012Metric
C609, C615: 10n; C_0603_1608Metric
C617: 100p; C_0603_1608Metric
C618, C619, C620, C621: 22u; C_1206_3216Metric
JP601: EN; SolderJumper-2_P1.3mm_Open_RoundedPad1.0x1.5mm
L601: 1u; 74438367010; MPN 74438367010
R601, R602, R604, R605, R611: 100k; R_0603_1608Metric
R603: 9.31k; R_0603_1608Metric
R606: 150k; R_0603_1608Metric
R607: 8.06k; R_0603_1608Metric
R608, R609: 10; R_0603_1608Metric
R610: 20m; PE1206FRE470R02L; MPN PE1206FRE470R02L
TP601, TP602: TestPoint; TestPoint_Pad_D1.0mm
U601: TPS552872RYQR; MPN TPS552872RYQR

Connections:
/Buck-Boost-1/VIN: C601.1, C602.1, C603.1, C604.1, C605.1, C606.1, C607.1, JP601.2 (B), U601.7 (VIN); also elsewhere on the board
/Buck-Boost-3/EN: R601.2, R602.1, U601.1 (EN/UVLO)
/Buck-Boost-3/FB_BT: R611.1, U601.14 (FB); also elsewhere on the board
/Buck-Boost-3/PG: R604.2, TP601.1, U601.3 (PG)
/Buck-Boost-3/VCC: C608.1, R604.1, R605.1, U601.2 (MODE), U601.18 (VCC)
/Buck-Boost-3/VOUT: R609.1, R610.2, R611.2; also elsewhere on the board
/Buck-Boost-3/~CC: R605.2, TP602.1, U601.4 (~CC)
GND: C601.2, C602.2, C603.2, C604.2, C605.2, C606.2, C607.2, C608.2, C609.2, C612.2, C614.2, C615.2, C616.2, C617.2, C618.2, C619.2, C620.2, C621.2, C622.2, R602.2, R603.2, R606.2, U601.9 (PGND), U601.17 (AGND); also elsewhere on the board
unnamed: C615.1, R607.2
unnamed: JP601.1 (A), R601.1
unnamed: C610.2, U601.20 (BOOT1)
unnamed: C611.2, U601.19 (BOOT2)
unnamed: R606.1, U601.16 (CDC)
unnamed: C617.1, R607.1, U601.15 (COMP)
unnamed: C609.1, U601.5 (DITH/SYNC)
unnamed: R603.1, U601.6 (FSW)
unnamed: C613.2, R609.2, U601.13 (ISN)
unnamed: C613.1, R608.2, U601.12 (ISP)
unnamed: C610.1, L601.1, U601.8 (SW1)
unnamed: C611.1, L601.2, U601.10 (SW2)
unnamed: C612.1, C614.1, C616.1, C618.1, C619.1, C620.1, C621.1, C622.1, R608.1, R610.1, U601.11 (VOUT)

Parts of its further copies:
C401, C422, C501, C522: 47u; 865080543009; MPN 865080543009; not fitted
C402, C403, C404, C502, C503, C504: 10u; C_0805_2012Metric
C405, C416, C505, C516: 1u; C_0603_1608Metric
C406, C407, C410, C411, C412, C413, C414, C506, C507, C510, C511, C512, C513, C514: 100n; C_0603_1608Metric
C408, C508: 4.7u; C_0805_2012Metric
C409, C415, C509, C515: 10n; C_0603_1608Metric
C417, C517: 100p; C_0603_1608Metric
C418, C419, C420, C421, C518, C519, C520, C521: 22u; C_1206_3216Metric
JP401, JP501: EN; SolderJumper-2_P1.3mm_Open_RoundedPad1.0x1.5mm
L401, L501: 1u; 74438367010; MPN 74438367010
R401, R402, R404, R405, R411, R501, R502, R504, R505, R511: 100k; R_0603_1608Metric
R403, R503: 9.31k; R_0603_1608Metric
R406, R506: 150k; R_0603_1608Metric
R407, R507: 8.06k; R_0603_1608Metric
R408, R409, R508, R509: 10; R_0603_1608Metric
R410, R510: 20m; PE1206FRE470R02L; MPN PE1206FRE470R02L
TP401, TP402, TP501, TP502: TestPoint; TestPoint_Pad_D1.0mm
U401, U501: TPS552872RYQR; MPN TPS552872RYQR

Connections of its further copies:
/Buck-Boost-1/EN: R401.2, R402.1, U401.1 (EN/UVLO)
/Buck-Boost-1/FB_BT: R411.1, U401.14 (FB); also elsewhere on the board
/Buck-Boost-1/PG: R404.2, TP401.1, U401.3 (PG)
/Buck-Boost-1/VCC: C408.1, R404.1, R405.1, U401.2 (MODE), U401.18 (VCC)
/Buck-Boost-1/VIN: C401.1, C402.1, C403.1, C404.1, C405.1, C406.1, C407.1, C501.1, C502.1, C503.1, C504.1, C505.1, C506.1, C507.1, JP401.2 (B), JP501.2 (B), U401.7 (VIN), U501.7 (VIN); also elsewhere on the board
/Buck-Boost-1/VOUT: R409.1, R410.2, R411.2; also elsewhere on the board
/Buck-Boost-1/~CC: R405.2, TP402.1, U401.4 (~CC)
/Buck-Boost-2/EN: R501.2, R502.1, U501.1 (EN/UVLO)
/Buck-Boost-2/FB_BT: R511.1, U501.14 (FB); also elsewhere on the board
/Buck-Boost-2/PG: R504.2, TP501.1, U501.3 (PG)
/Buck-Boost-2/VCC: C508.1, R504.1, R505.1, U501.2 (MODE), U501.18 (VCC)
/Buck-Boost-2/VOUT: R509.1, R510.2, R511.2; also elsewhere on the board
/Buck-Boost-2/~CC: R505.2, TP502.1, U501.4 (~CC)
GND: C401.2, C402.2, C403.2, C404.2, C405.2, C406.2, C407.2, C408.2, C409.2, C412.2, C414.2, C415.2, C416.2, C417.2, C418.2, C419.2, C420.2, C421.2, C422.2, C501.2, C502.2, C503.2, C504.2, C505.2, C506.2, C507.2, C508.2, C509.2, C512.2, C514.2, C515.2, C516.2, C517.2, C518.2, C519.2, C520.2, C521.2, C522.2, R402.2, R403.2, R406.2, R502.2, R503.2, R506.2, U401.9 (PGND), U401.17 (AGND), U501.9 (PGND), U501.17 (AGND); also elsewhere on the board
unnamed: C415.1, R407.2
unnamed: C515.1, R507.2
unnamed: JP401.1 (A), R401.1
unnamed: JP501.1 (A), R501.1
unnamed: C410.2, U401.20 (BOOT1)
unnamed: C411.2, U401.19 (BOOT2)
unnamed: R406.1, U401.16 (CDC)
unnamed: C417.1, R407.1, U401.15 (COMP)
unnamed: C409.1, U401.5 (DITH/SYNC)
unnamed: R403.1, U401.6 (FSW)
unnamed: C413.2, R409.2, U401.13 (ISN)
unnamed: C413.1, R408.2, U401.12 (ISP)
unnamed: C410.1, L401.1, U401.8 (SW1)
unnamed: C411.1, L401.2, U401.10 (SW2)
unnamed: C412.1, C414.1, C416.1, C418.1, C419.1, C420.1, C421.1, C422.1, R408.1, R410.1, U401.11 (VOUT)
unnamed: C510.2, U501.20 (BOOT1)
unnamed: C511.2, U501.19 (BOOT2)
unnamed: R506.1, U501.16 (CDC)
unnamed: C517.1, R507.1, U501.15 (COMP)
unnamed: C509.1, U501.5 (DITH/SYNC)
unnamed: R503.1, U501.6 (FSW)
unnamed: C513.2, R509.2, U501.13 (ISN)
unnamed: C513.1, R508.2, U501.12 (ISP)
unnamed: C510.1, L501.1, U501.8 (SW1)
unnamed: C511.1, L501.2, U501.10 (SW2)
unnamed: C512.1, C514.1, C516.1, C518.1, C519.1, C520.1, C521.1, C522.1, R508.1, R510.1, U501.11 (VOUT)

Notes on the sheet:
1.2*100k R_{FB_BT} = --------- V_{OUT} - 1.2
ex. V_{OUT} = 12V, R_{FB_BT} = 11.1k
V_{REF}*R_{FB_UP} R_{FB_BT} = --------- V_{OUT} - V_{REF}
Enable
Buck-Boost Converter
Test Points
Note: To set output voltage, V_{OUT}, connect 'FB_BT' through R_{FB_BT} to ground to set output voltage.

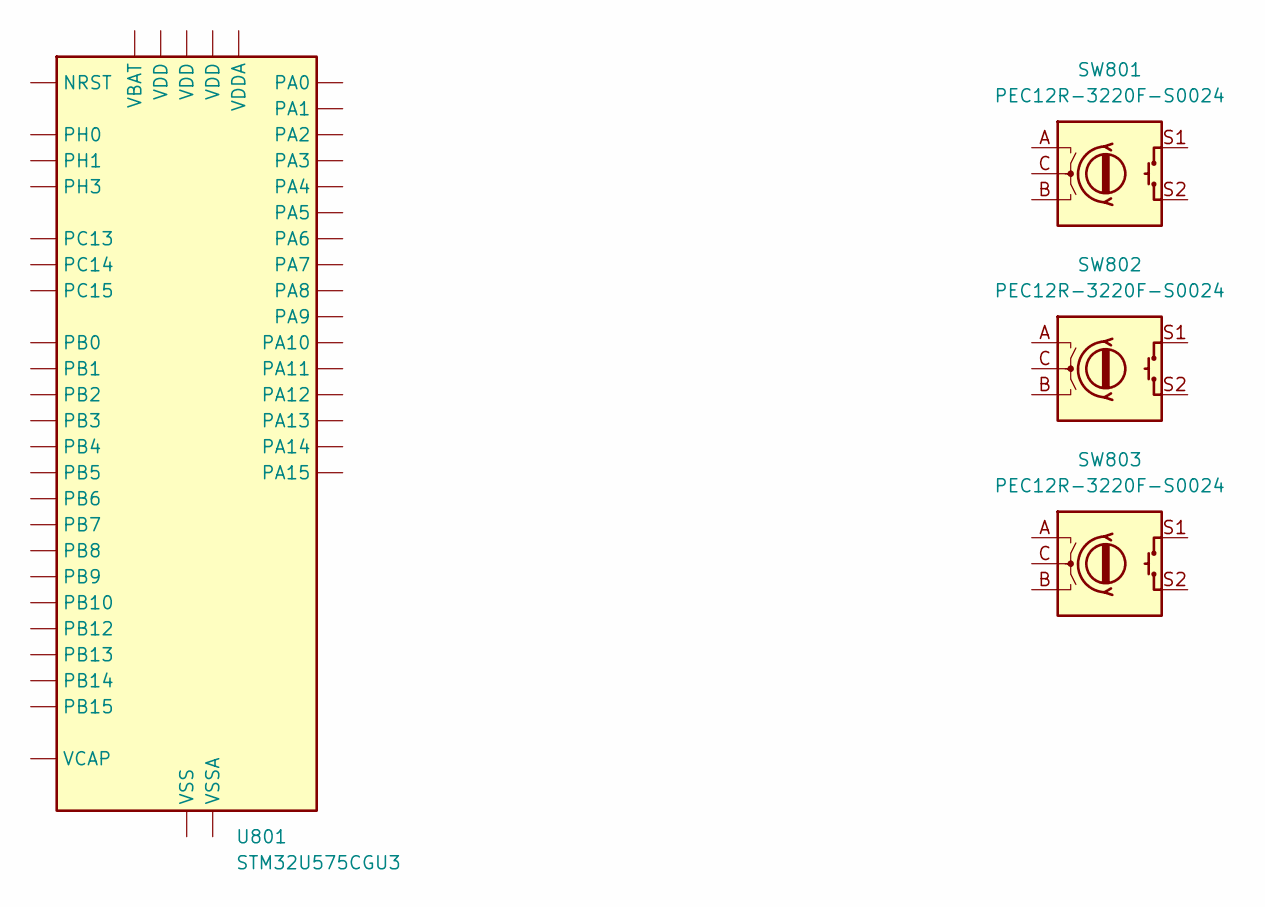
[picture p82: schematic microcontroller.kicad_sch, Power Supply]

Parts:
SW801, SW802, SW803: MPN PEC12R-3220F-S0024
U801: MPN STM32U575CGU3

Connections:
unnamed: U801.23 (VSS), U801.35 (VSS), U801.47 (VSS), U801.49 (VSS)

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
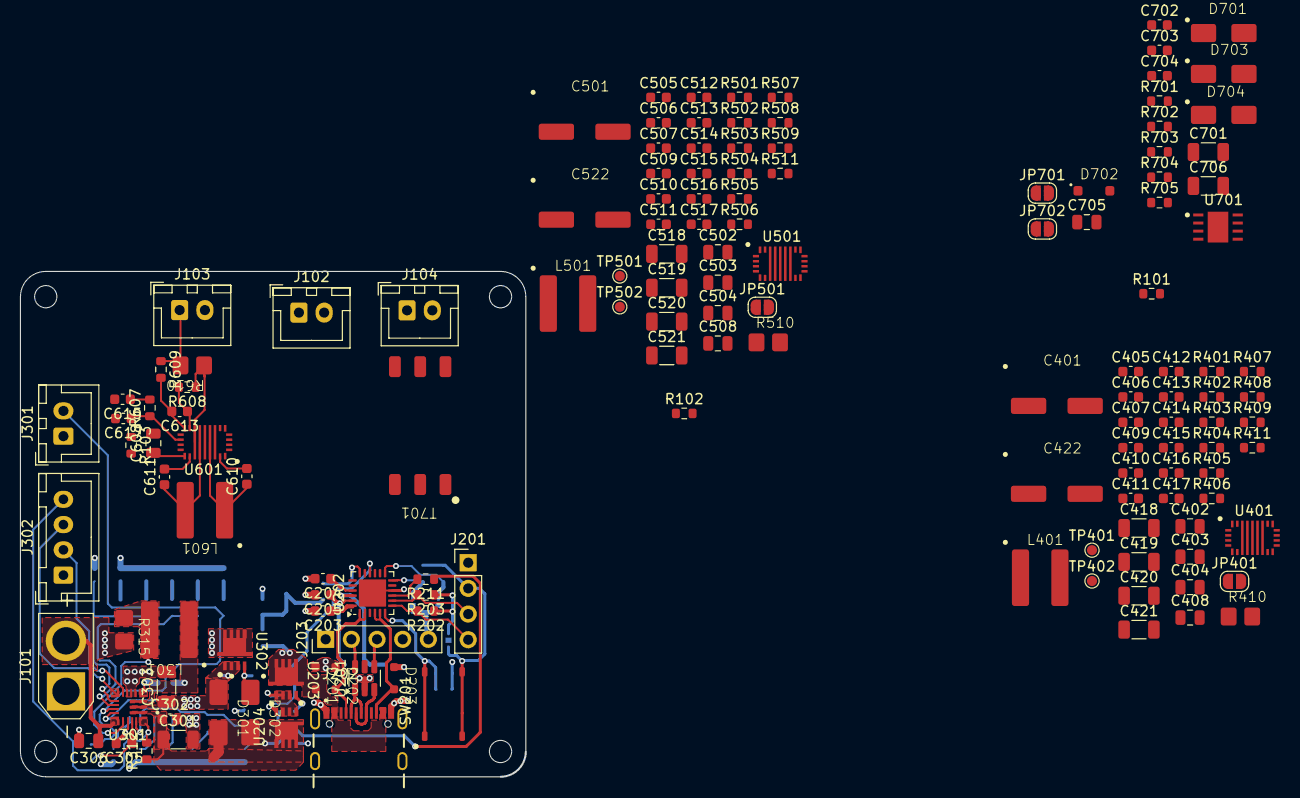
[picture p83: board controller.kicad_pcb from above]

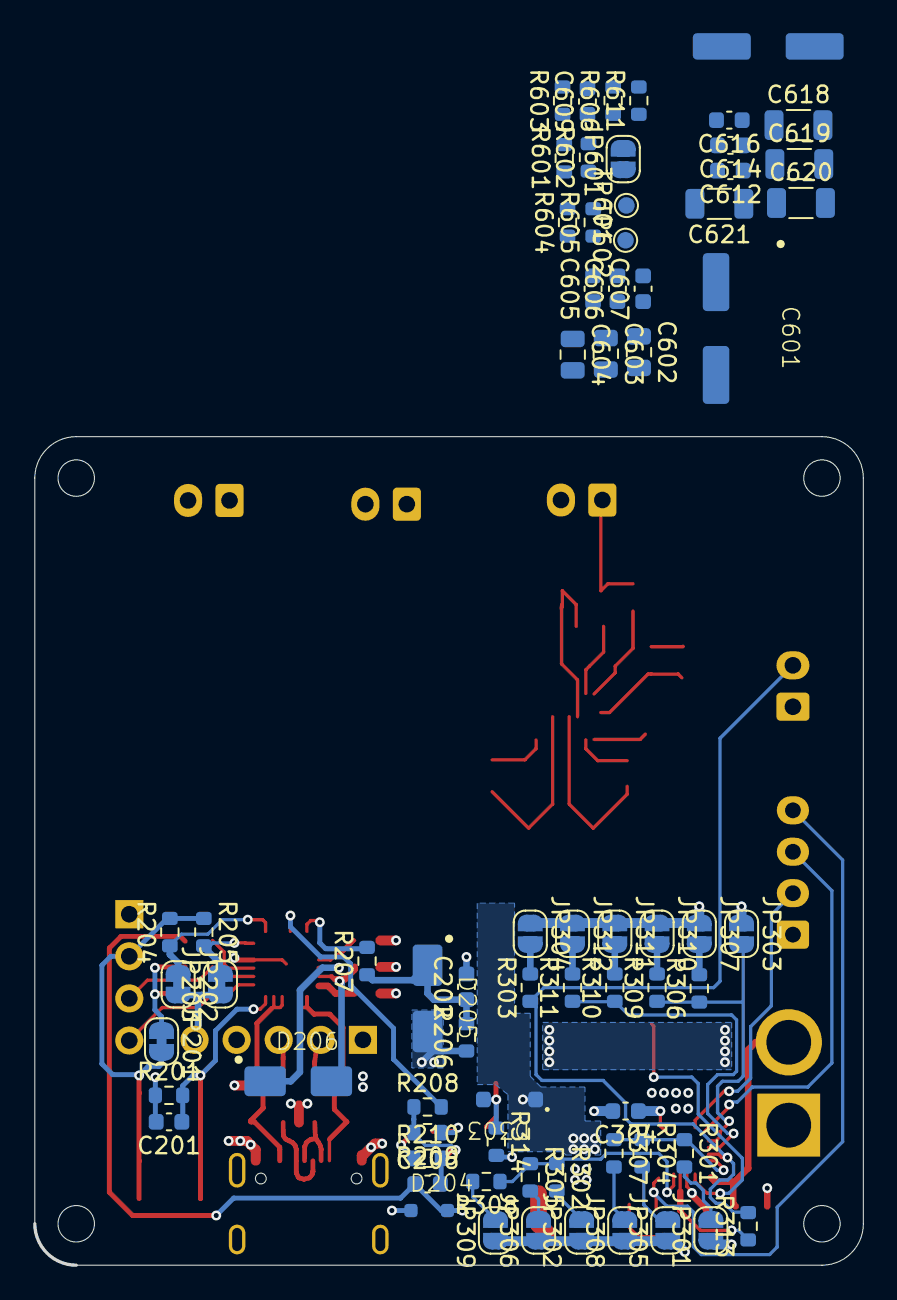
[picture p84: board controller.kicad_pcb from below]

Board: 4 copper layers, 50.0 x 50.0 mm, 215 parts (70 on the bottom side), 118 nets.
