nicholasnloehrke/87s_research/kicad/power_supply/isolated_dc_to_dc.kicad_sch

## KiCad design kicad/power_supply/isolated_dc_to_dc.kicad_sch (2024-10-25)

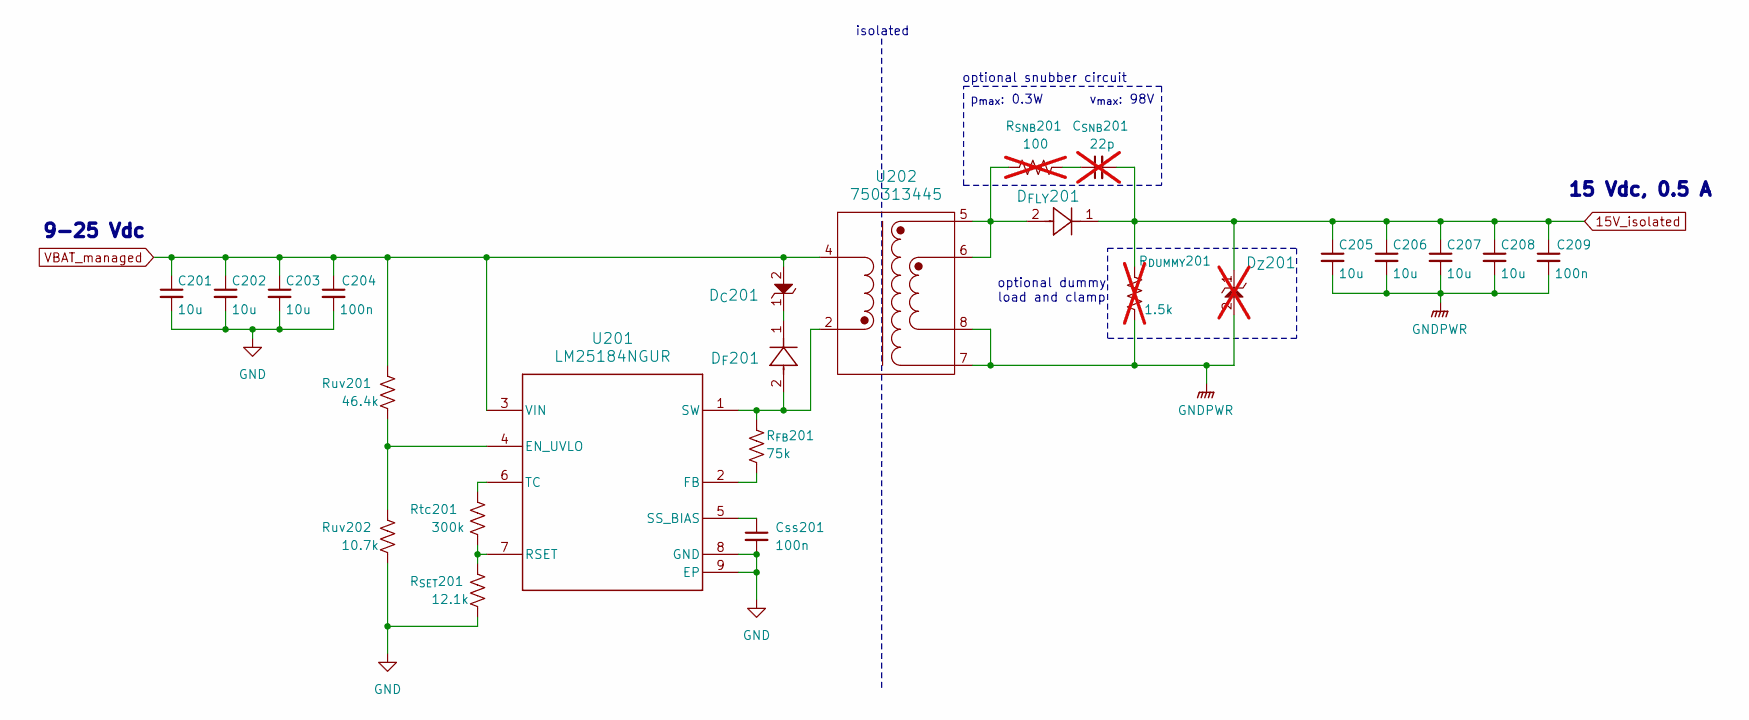
[picture p88: schematic isolated_dc_to_dc.kicad_sch]

Parts:
C201, C202, C203, C205, C206, C207, C208: 10u; C_1206_3216Metric
C204, C209: 100n; C_0402_1005Metric
C_{SNB}201: 22p; C_0402_1005Metric; not fitted
Css201: 100n; C_0402_1005Metric
D_{C}201: PDZVTR9.1B; DIO_PDZVTFT_ROM
D_{FLY}201: SK510A-LTP; SMADO-214AC_LEAD-FRAME_MCC
D_{F}201: SK510A-LTP; SMADO-214AC_LEAD-FRAME_MCC
D_{Z}201: PDZVTR9.1B; DIO_PDZVTFT_ROM; not fitted
R_{DUMMY}201: 1.5k; R_0402_1005Metric; not fitted
R_{FB}201: 75k; R_0402_1005Metric
R_{SET}201: 12.1k; R_0402_1005Metric
R_{SNB}201: 100; R_0402_1005Metric; not fitted
Rtc201: 300k; R_0402_1005Metric
Ruv201: 46.4k; R_0402_1005Metric
Ruv202: 10.7k; R_0402_1005Metric
U201: LM25184NGUR; NGU0008C-IPC_A
U202: 750313445; SOIC_13445_WRE

Connections:
15V_isolated: C205.1, C206.1, C207.1, C208.1, C209.1, C_{SNB}201.2, D_{FLY}201.1, D_{Z}201.1, R_{DUMMY}201.2
GND: C201.2, C202.2, C203.2, C204.2, Css201.2, R_{SET}201.2, Ruv202.2, U201.8 (GND), U201.9 (EP)
GNDPWR: C205.2, C206.2, C207.2, C208.2, C209.2, D_{Z}201.2, R_{DUMMY}201.1, U202.7, U202.8
unnamed: C_{SNB}201.1, R_{SNB}201.2
unnamed: Css201.1, U201.5 (SS_BIAS)
unnamed: D_{C}201.1, D_{F}201.1
unnamed: D_{FLY}201.2, R_{SNB}201.1, U202.5, U202.6
unnamed: D_{F}201.2, R_{FB}201.1, U201.1 (SW), U202.2
unnamed: R_{FB}201.2, U201.2 (FB)
unnamed: R_{SET}201.1, Rtc201.2, U201.7 (RSET)
unnamed: Rtc201.1, U201.6 (TC)
unnamed: Ruv201.2, Ruv202.1, U201.4 (EN_UVLO)
VBAT_managed: C201.1, C202.1, C203.1, C204.1, D_{C}201.2, Ruv201.1, U201.3 (VIN), U202.4

Notes on the sheet:
optional snubber circuit
optional dummy load and clamp
9-25 Vdc
isolated
p_{max}: 0.3W
15 Vdc, 0.5 A
v_{max}: 98V
