nicholasnloehrke/87s_research/kicad/power_supply/switching_channel.kicad_sch

## KiCad design kicad/power_supply/switching_channel.kicad_sch (2024-10-03)

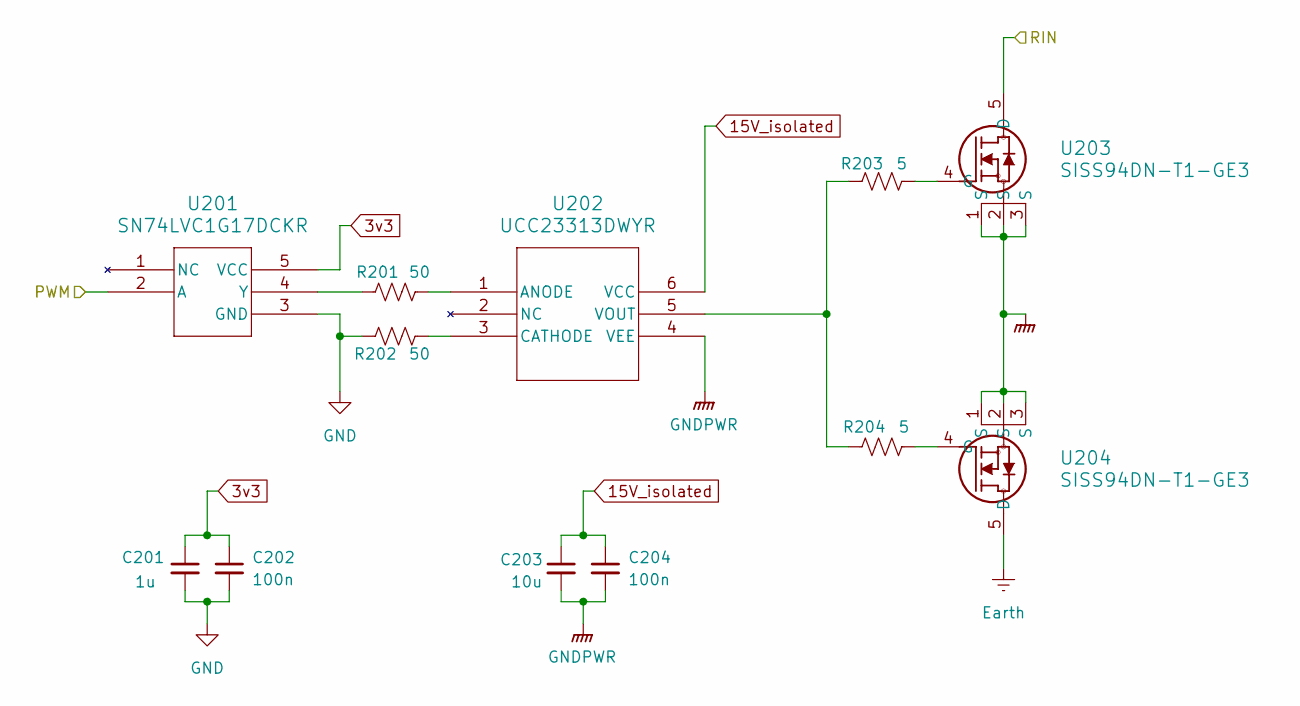
[picture p89: schematic switching_channel.kicad_sch]

Parts:
C201: 1u; C_0603_1608Metric
C202, C204: 100n; C_0402_1005Metric
C203: 10u; C_1206_3216Metric
R201, R202: 50; R_0402_1005Metric_Pad0.72x0.64mm_HandSolder
R203, R204: 5; R_0603_1608Metric_Pad0.98x0.95mm_HandSolder
U201: SN74LVC1G17DCKR; DCK5
U202: UCC23313DWYR; SOIC6_DWY_TEX
U203, U204: SISS94DN-T1-GE3; MOSFET_3DN-T1-GE3_VIS

Connections:
3v3: C201.1, C202.1, U201.5 (VCC)
15V_isolated: C203.1, C204.1, U202.6 (VCC)
Earth: U204.5 (D)
GND: C201.2, C202.2, R202.1, U201.3 (GND)
GNDPWR: C203.2, C204.2, U202.4 (VEE), U203.1 (S), U203.2 (S), U203.3 (S), U204.1 (S), U204.2 (S), U204.3 (S)
unnamed: R201.1, U201.4 (Y)
unnamed: R201.2, U202.1 (ANODE)
unnamed: R202.2, U202.3 (CATHODE)
unnamed: R203.1, R204.1, U202.5 (VOUT)
unnamed: R203.2, U203.4 (G)
unnamed: R204.2, U204.4 (G)
PWM: U201.2 (A)
RIN: U203.5 (D)
